nhaynes84/roam/roam-touch/cad/out/bracer_pack_shot_iso.png

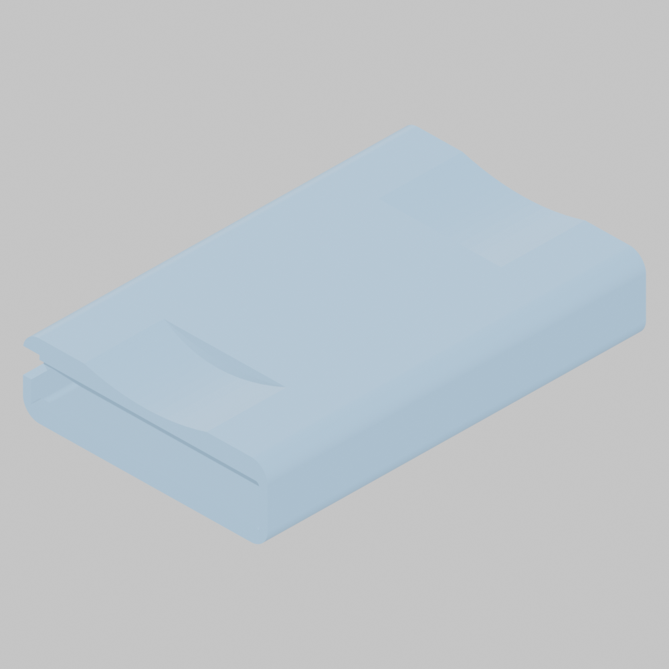
roam-touch/cad/out/bracer_pack_shot_iso.png
