nhaynes84/roam/roam-touch/cad/out/bracer_pack_shot_right.png

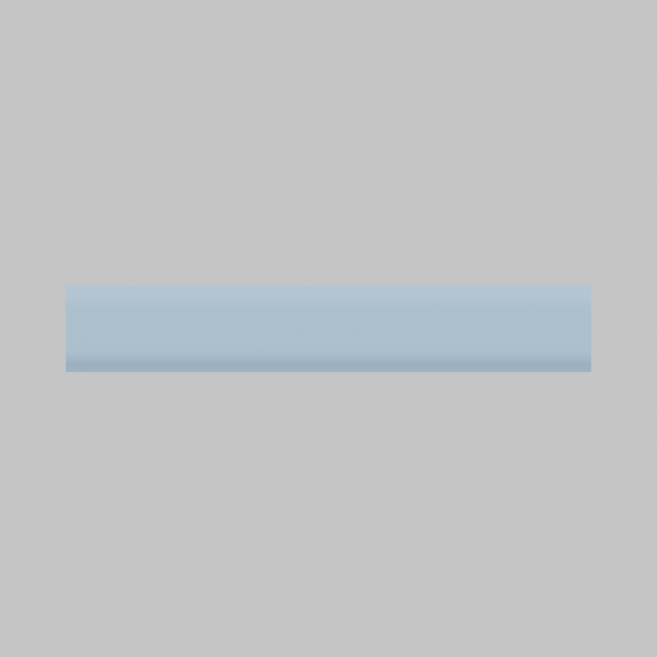
roam-touch/cad/out/bracer_pack_shot_right.png
