nhaynes84/roam/roam-touch/cad/out/bracer_pack_shot_top.png

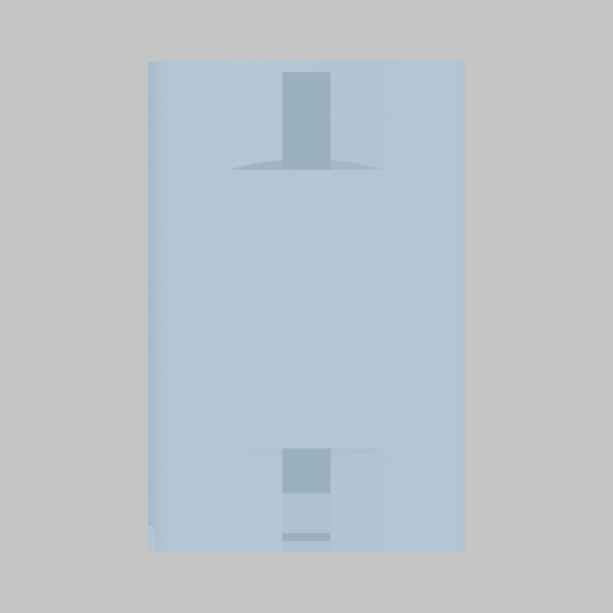
roam-touch/cad/out/bracer_pack_shot_top.png
