nhaynes84/roam/roam-touch/cad/out/landscape_shot_iso.png

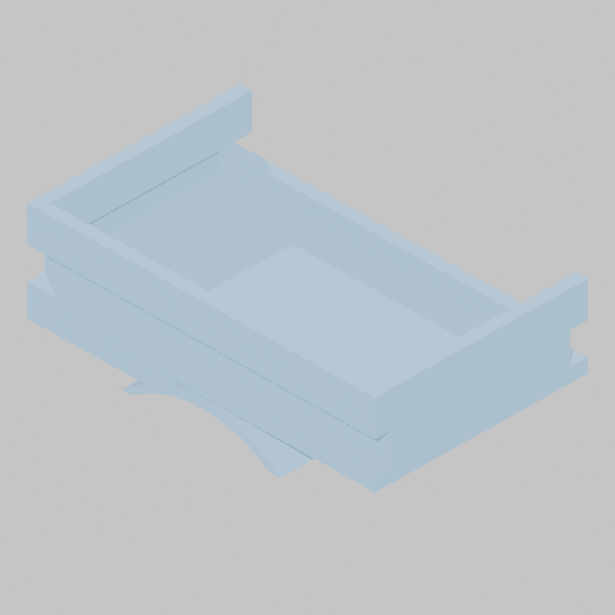
roam-touch/cad/out/landscape_shot_iso.png
