nhaynes84/roam/roam-touch/cad/out/landscape_shot_top.png

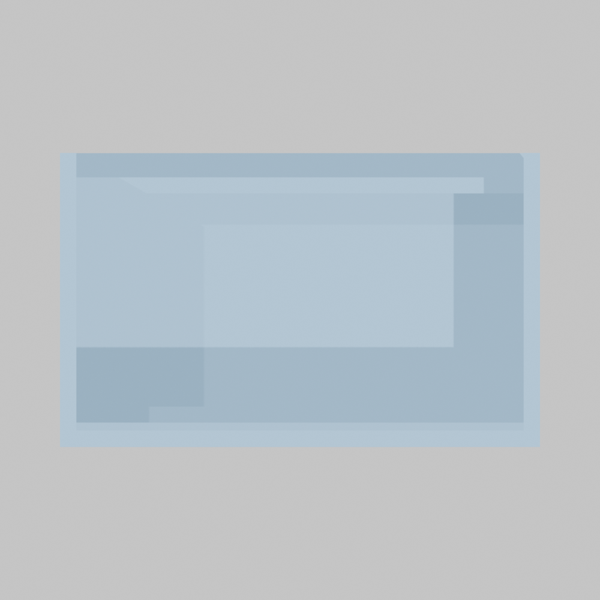
roam-touch/cad/out/landscape_shot_top.png
