nhaynes84/roam/roam-touch/cad/out/view_asm_bow.png

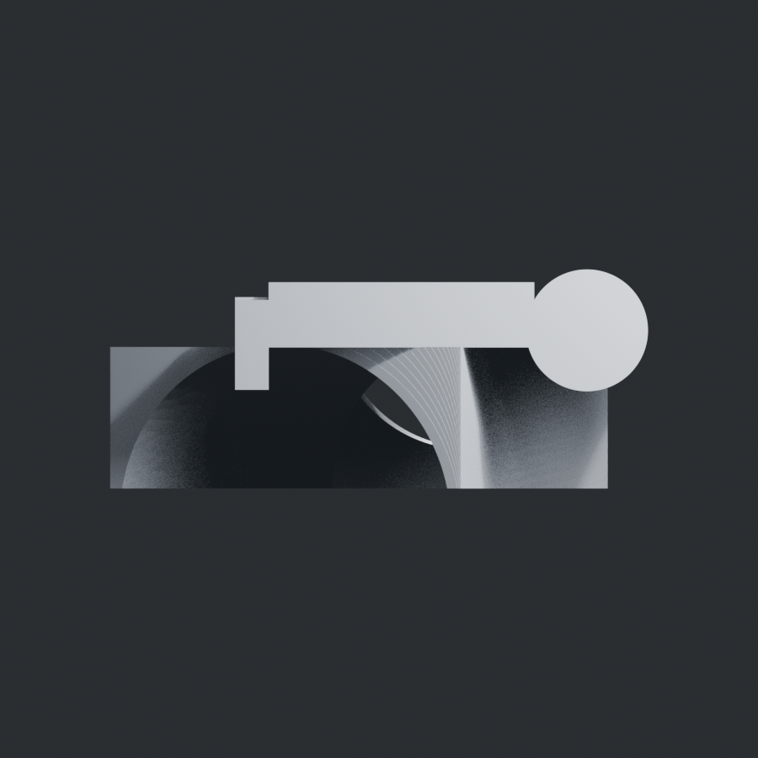
roam-touch/cad/out/view_asm_bow.png
