nhaynes84/roam/roam-touch/cad/out/view_asm_iso.png

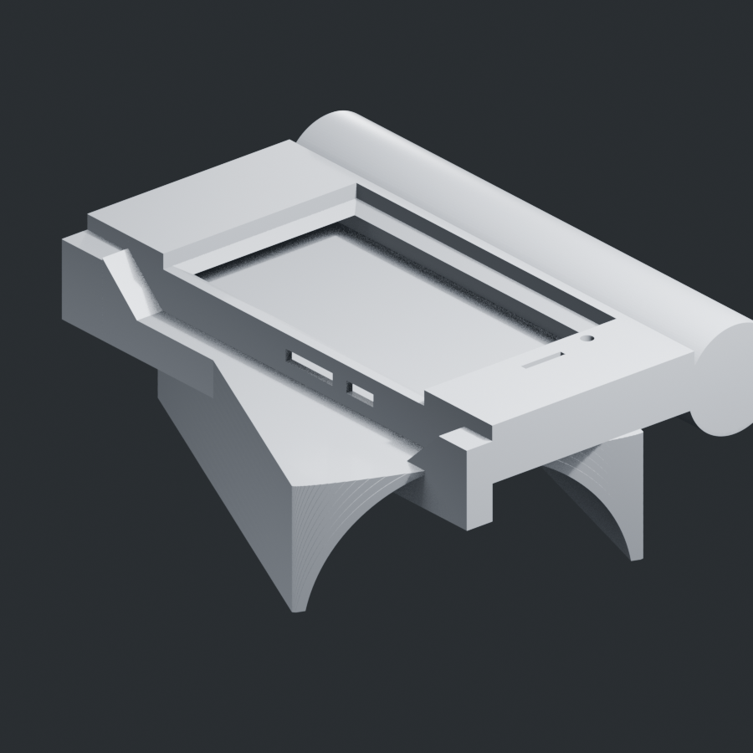
roam-touch/cad/out/view_asm_iso.png
