nhaynes84/roam/roam-touch/cad/out/view_asm_stbd.png

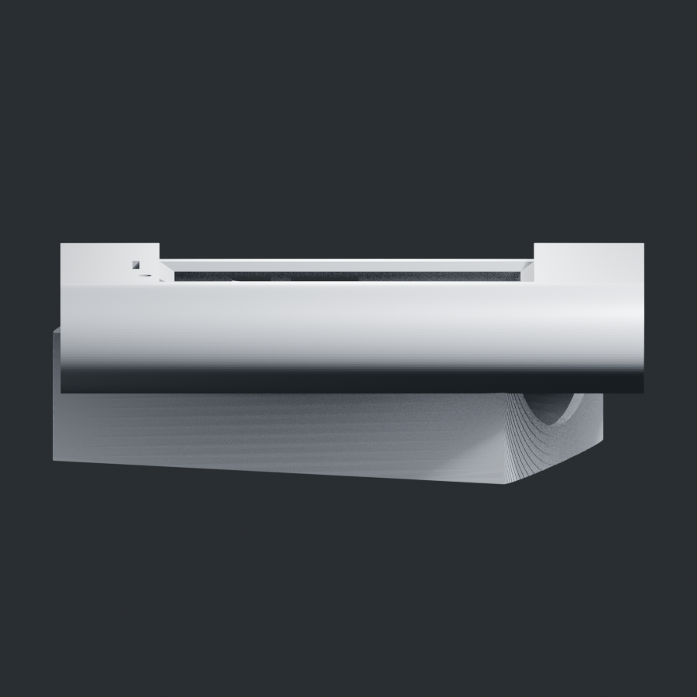
roam-touch/cad/out/view_asm_stbd.png
