nhaynes84/roam/roam-touch/cad/out/view_asm_stern.png

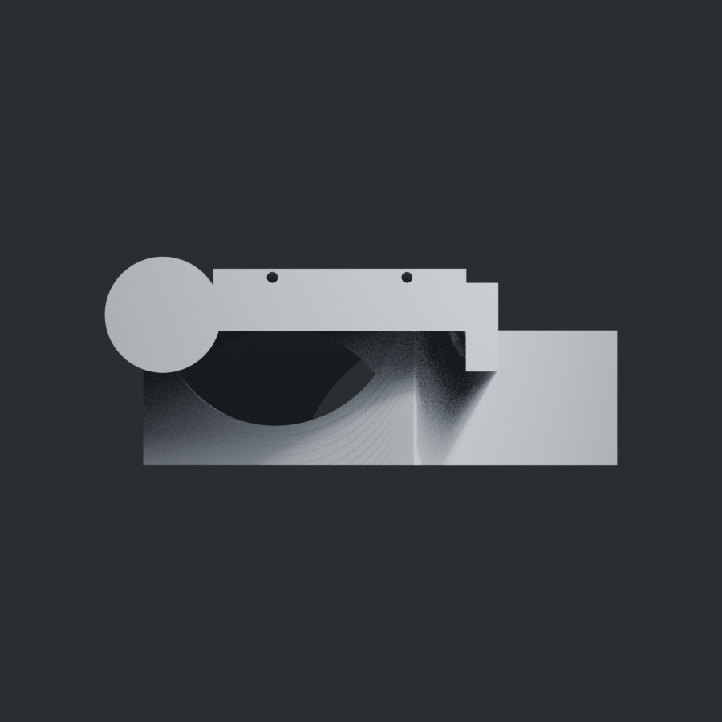
roam-touch/cad/out/view_asm_stern.png
