nhaynes84/roam/roam-touch/cad/out/view_asm_under.png

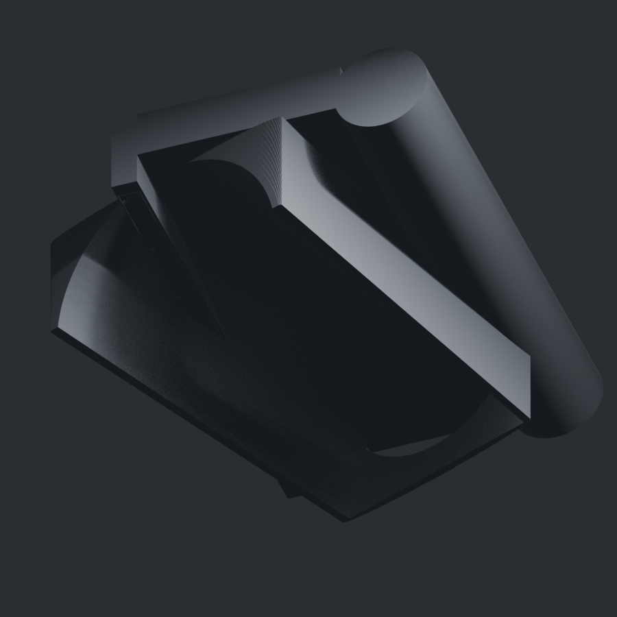
roam-touch/cad/out/view_asm_under.png
