nhaynes84/roam/roam-touch/cad/out/view_band_bow.png

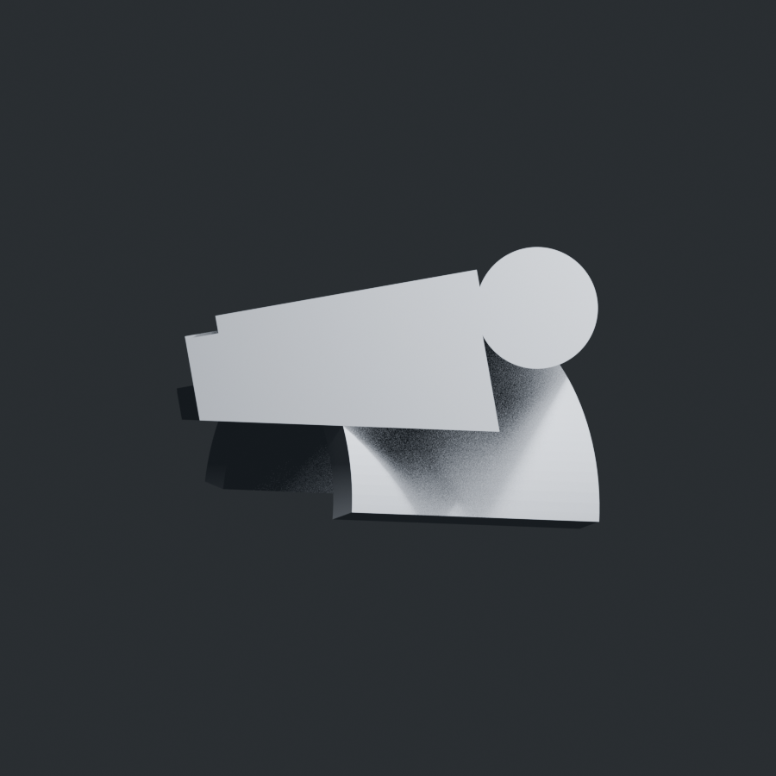
roam-touch/cad/out/view_band_bow.png
