nhaynes84/roam/roam-touch/cad/out/view_band_end.png

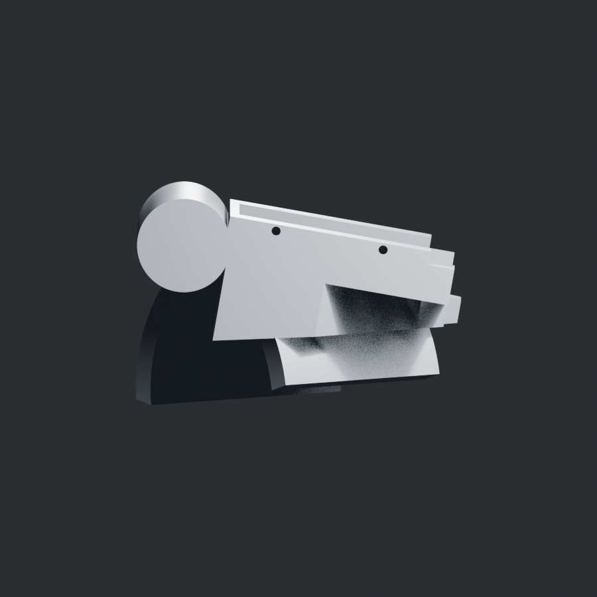
roam-touch/cad/out/view_band_end.png
