nhaynes84/roam/roam-touch/cad/out/view_band_iso.png

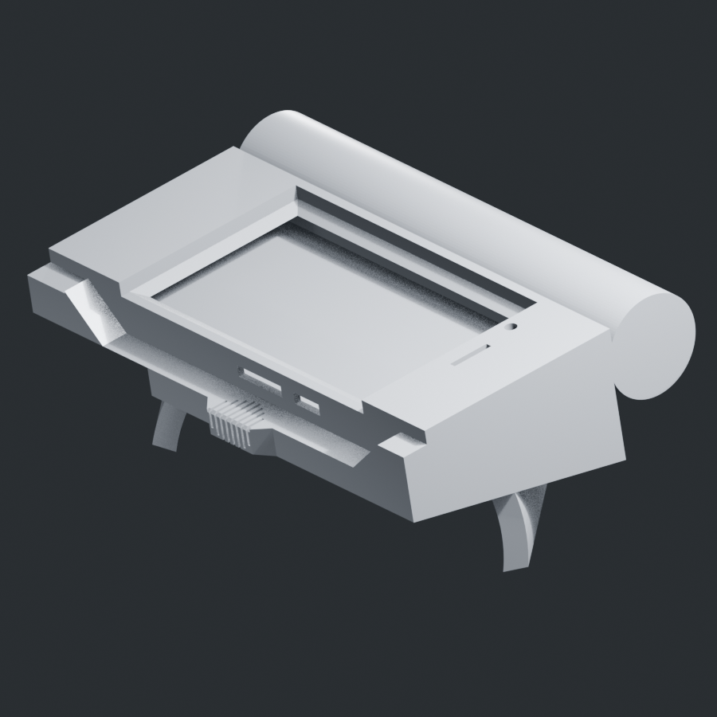
roam-touch/cad/out/view_band_iso.png
