nhaynes84/roam/roam-touch/cad/out/view_cap.png

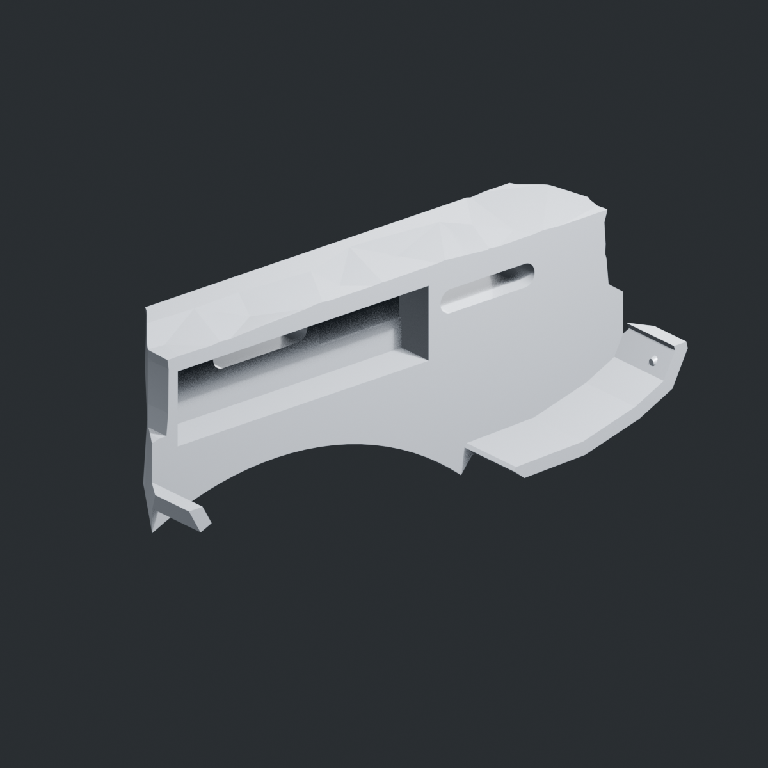
roam-touch/cad/out/view_cap.png
