nhaynes84/roam/roam-touch/cad/out/view_cc_end.png

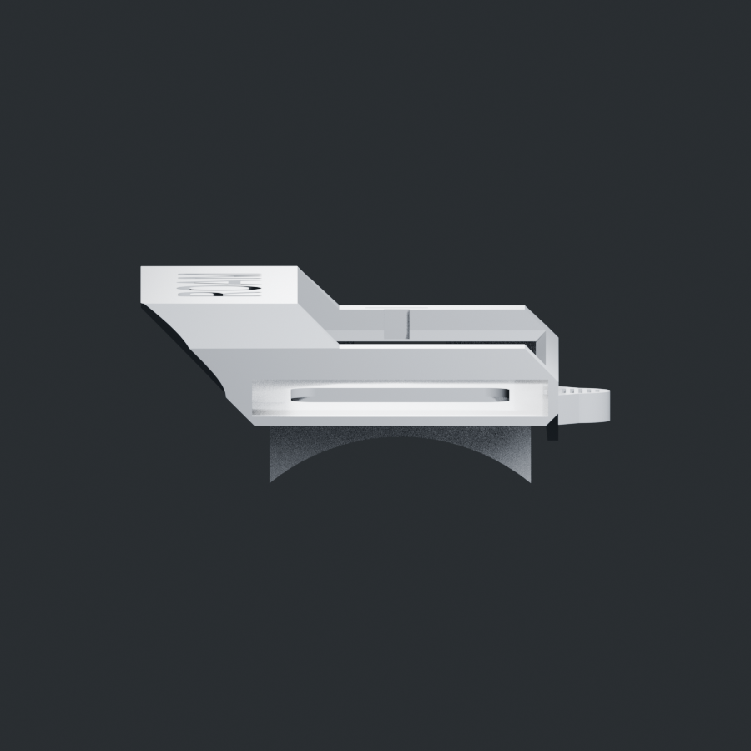
roam-touch/cad/out/view_cc_end.png
