nhaynes84/roam/roam-touch/cad/out/view_cc_iso.png

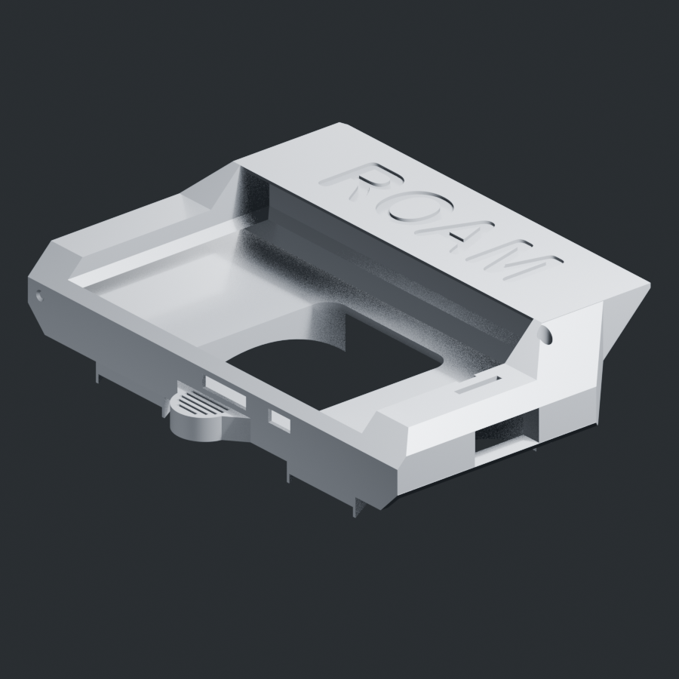
roam-touch/cad/out/view_cc_iso.png
