nhaynes84/roam/roam-touch/cad/out/view_cc_top.png

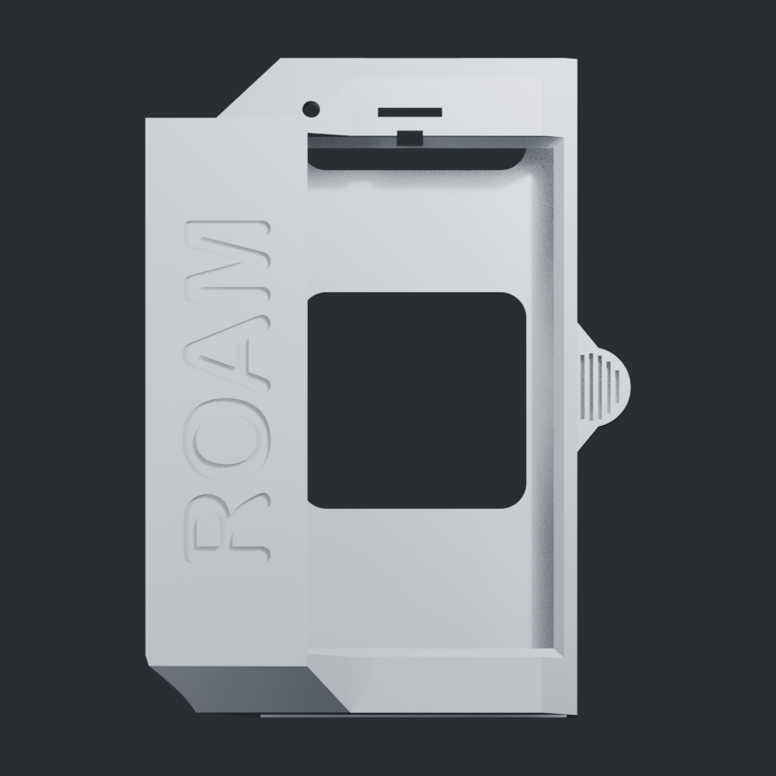
roam-touch/cad/out/view_cc_top.png
