nhaynes84/roam/roam-touch/cad/out/view_cov_open_e.png

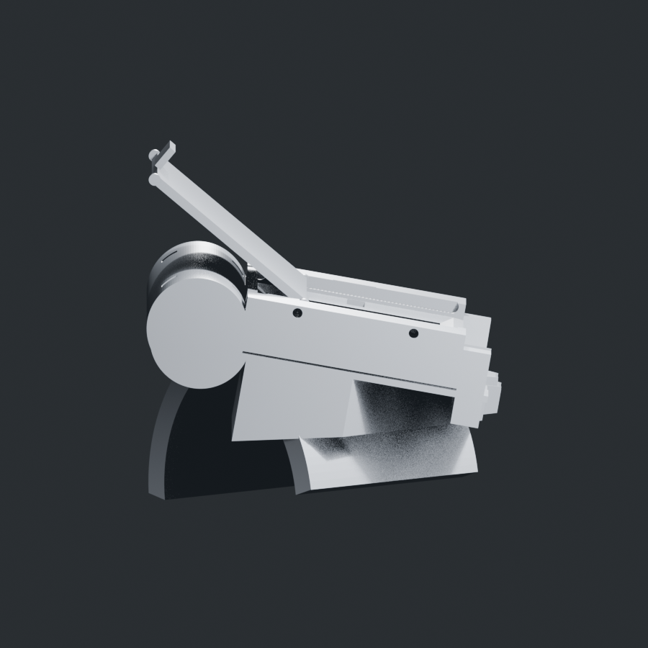
roam-touch/cad/out/view_cov_open_e.png
