nhaynes84/roam/roam-touch/cad/out/view_cov_open_i.png

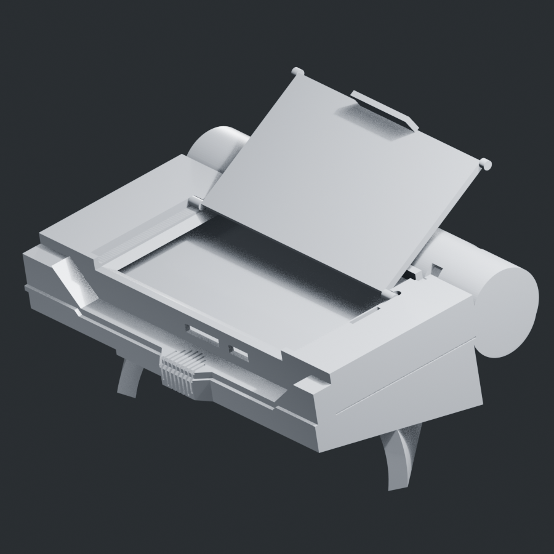
roam-touch/cad/out/view_cov_open_i.png
