nhaynes84/roam/roam-touch/cad/out/view_cuff_bow.png

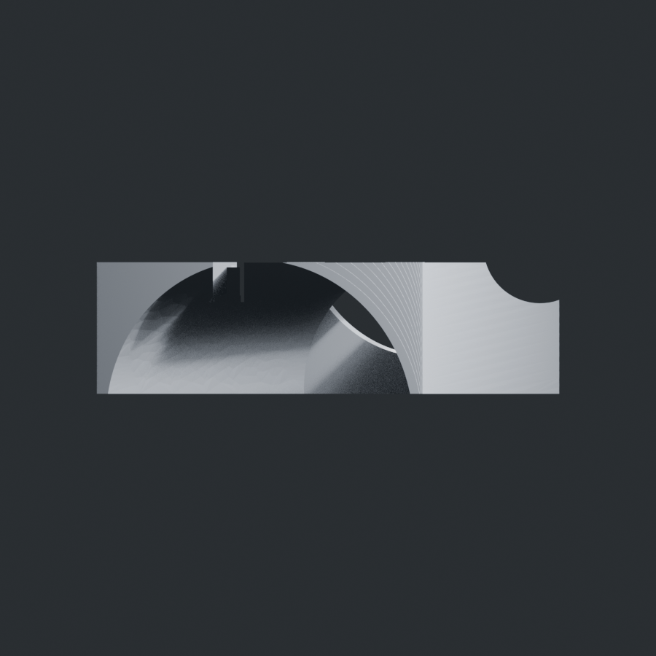
roam-touch/cad/out/view_cuff_bow.png
