nhaynes84/roam/roam-touch/cad/out/view_cuff_iso.png

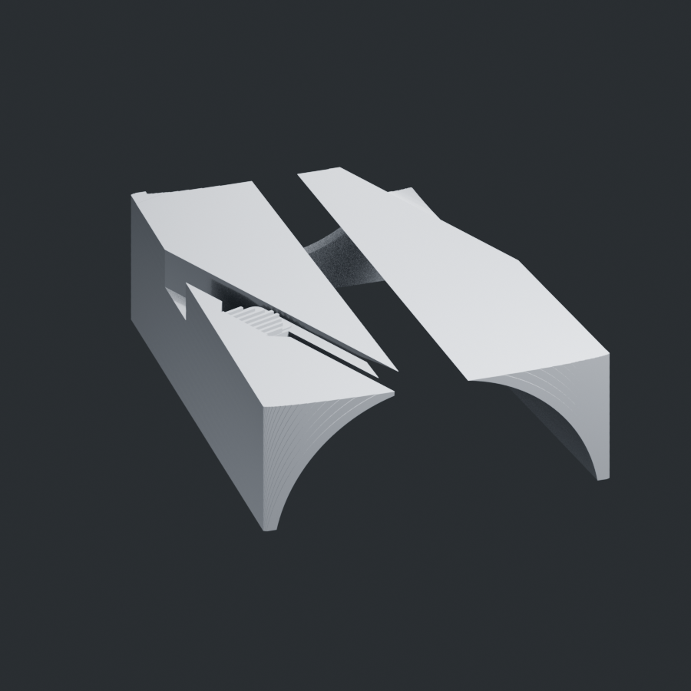
roam-touch/cad/out/view_cuff_iso.png
