nhaynes84/roam/roam-touch/cad/out/view_end_elbow.png

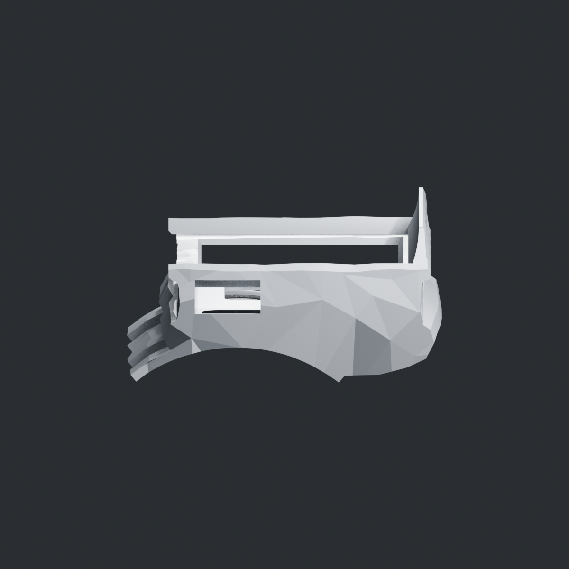
roam-touch/cad/out/view_end_elbow.png
