nhaynes84/roam/roam-touch/cad/out/view_end_elbow_q.png

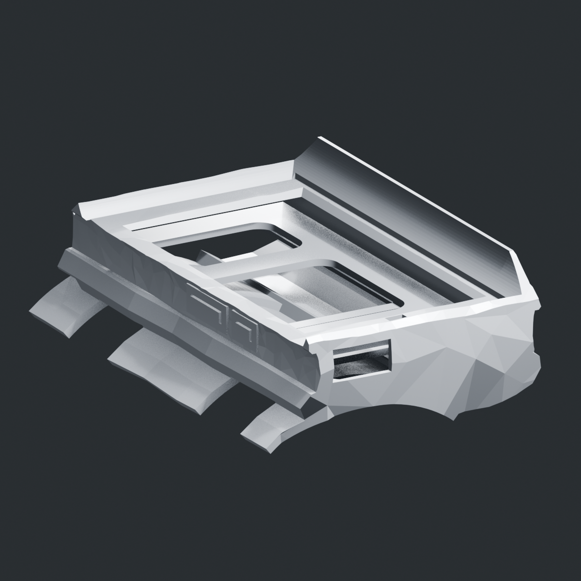
roam-touch/cad/out/view_end_elbow_q.png
