nhaynes84/roam/roam-touch/cad/out/view_end_wrist.png

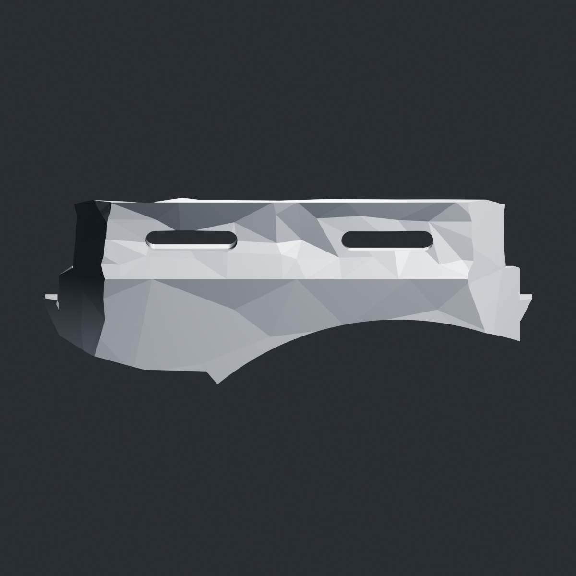
roam-touch/cad/out/view_end_wrist.png
