nhaynes84/roam/roam-touch/cad/out/view_guard_side.png

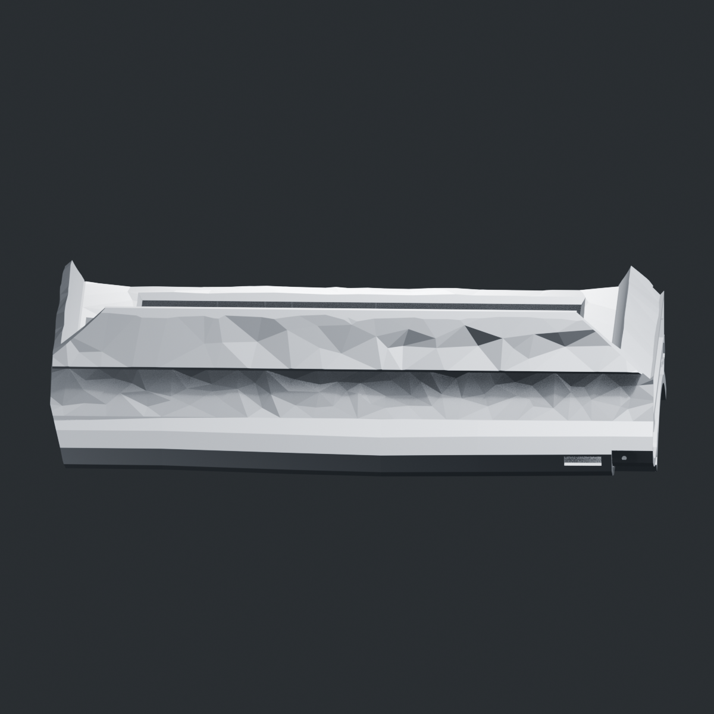
roam-touch/cad/out/view_guard_side.png
