nhaynes84/roam/roam-touch/cad/out/view_hg_iso.png

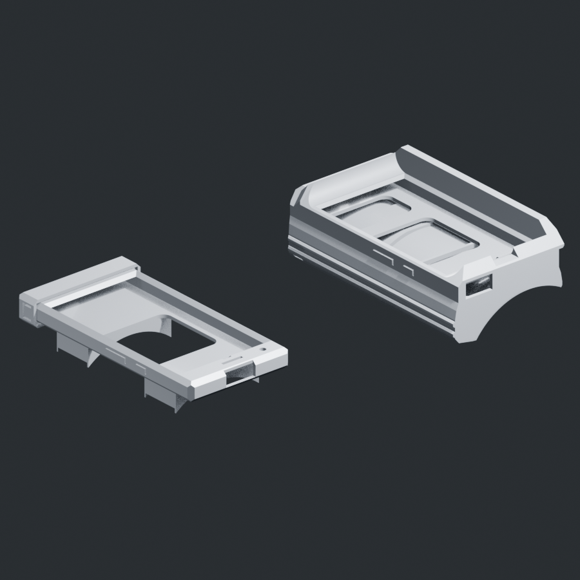
roam-touch/cad/out/view_hg_iso.png
