nhaynes84/roam/roam-touch/cad/out/view_hg_top.png

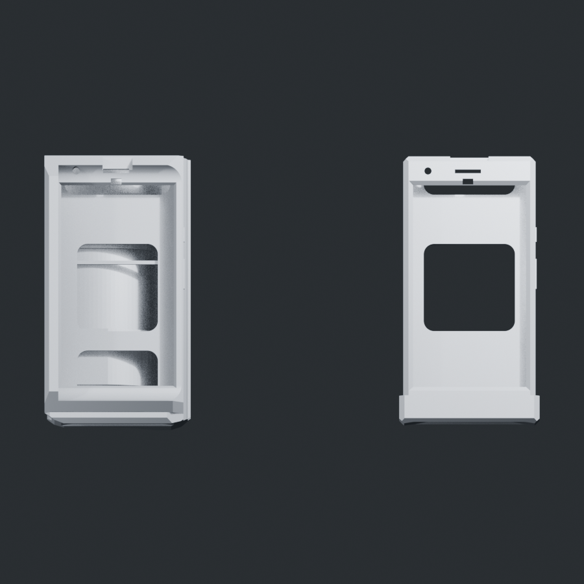
roam-touch/cad/out/view_hg_top.png
