nhaynes84/roam/roam-touch/cad/out/view_mic_q.png

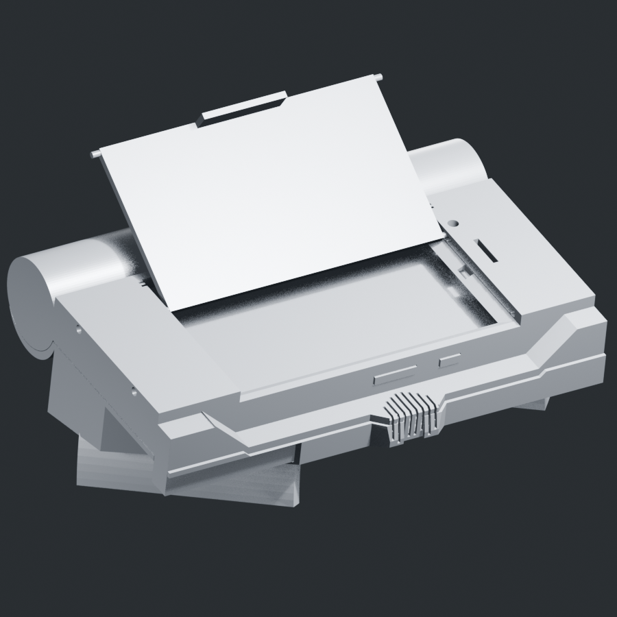
roam-touch/cad/out/view_mic_q.png
