nhaynes84/roam/roam-touch/cad/out/view_mic_sb.png

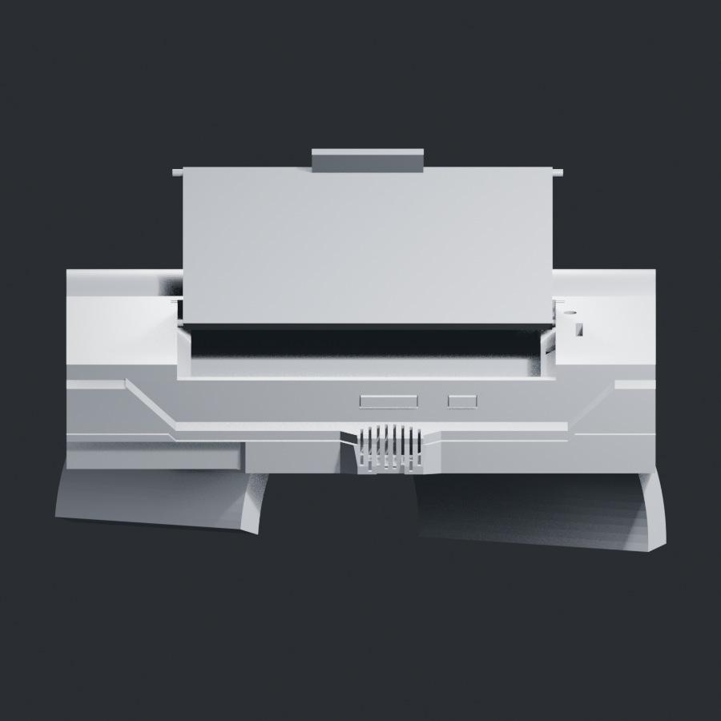
roam-touch/cad/out/view_mic_sb.png
