nhaynes84/roam/roam-touch/cad/out/view_pack_iso.png

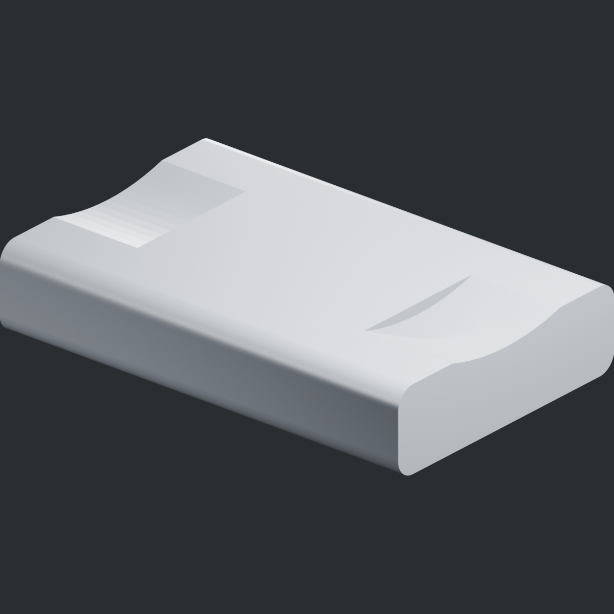
roam-touch/cad/out/view_pack_iso.png
