nhaynes84/roam/roam-touch/cad/out/view_roam1_btn.png

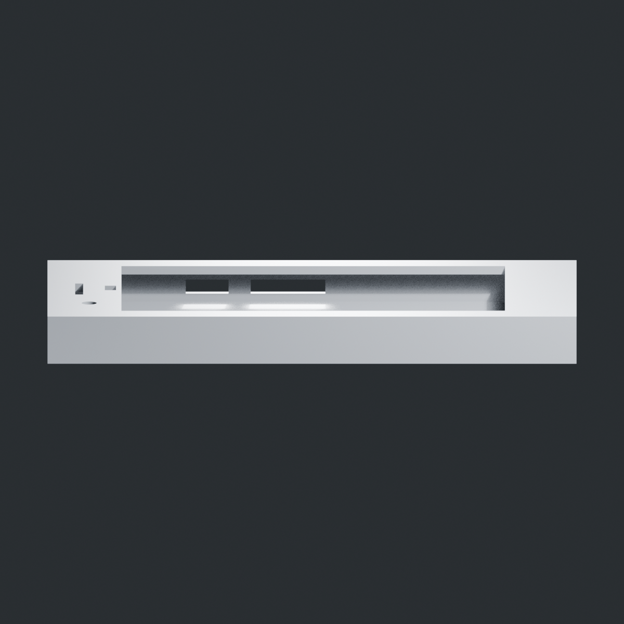
roam-touch/cad/out/view_roam1_btn.png
