nhaynes84/roam/roam-touch/cad/out/view_roam1_iso.png

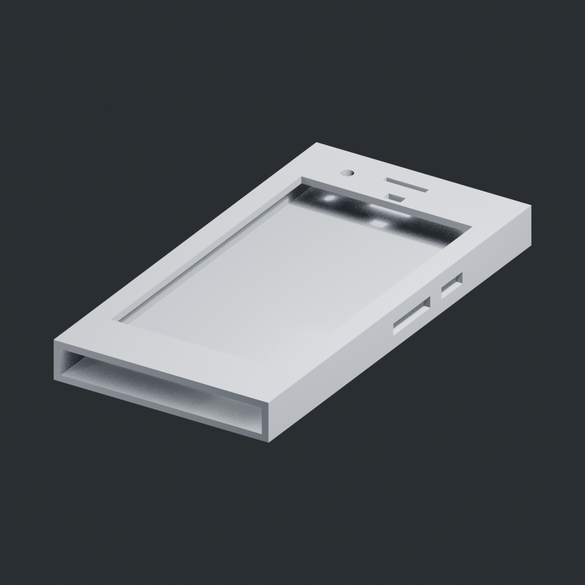
roam-touch/cad/out/view_roam1_iso.png
