nhaynes84/roam/roam-touch/cad/out/view_roam1_jack.png

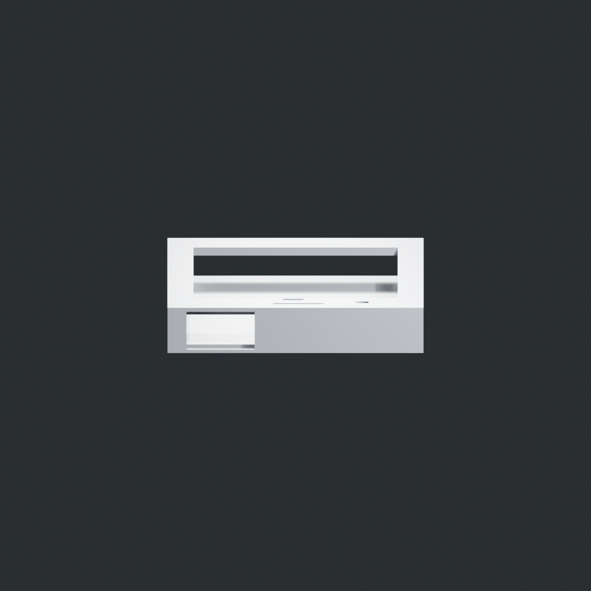
roam-touch/cad/out/view_roam1_jack.png
