nhaynes84/roam/roam-touch/cad/out/view_roam1_top.png

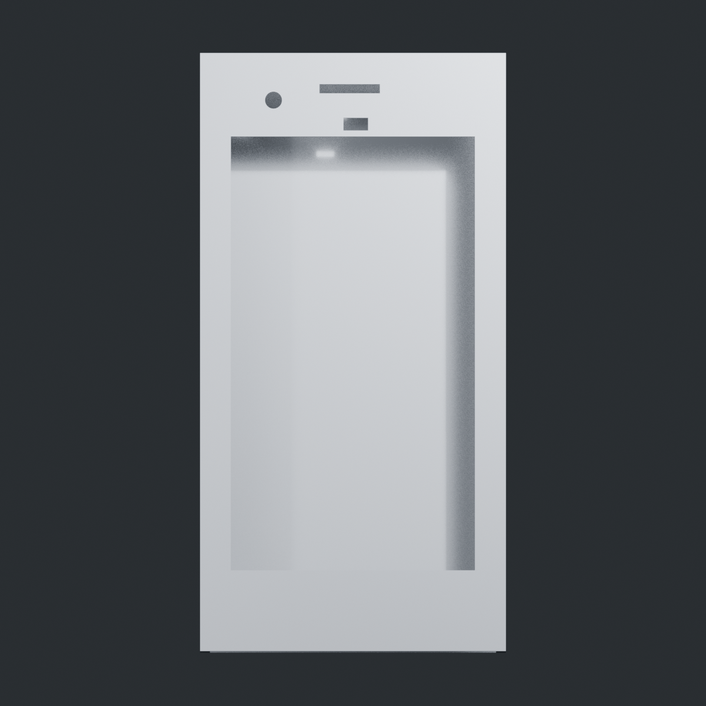
roam-touch/cad/out/view_roam1_top.png
