nhaynes84/roam/roam-touch/cad/out/view_roam1_usb.png

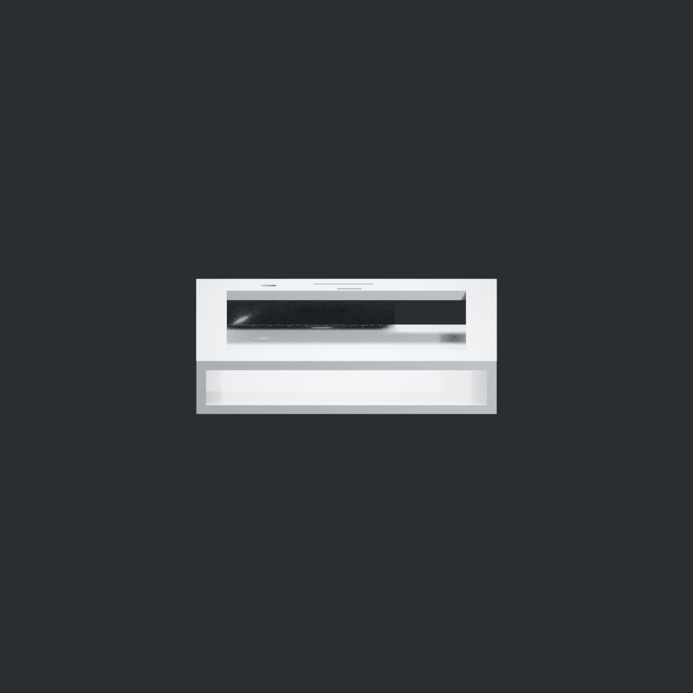
roam-touch/cad/out/view_roam1_usb.png
