nhaynes84/roam/roam-touch/cad/out/view_roam2_end.png

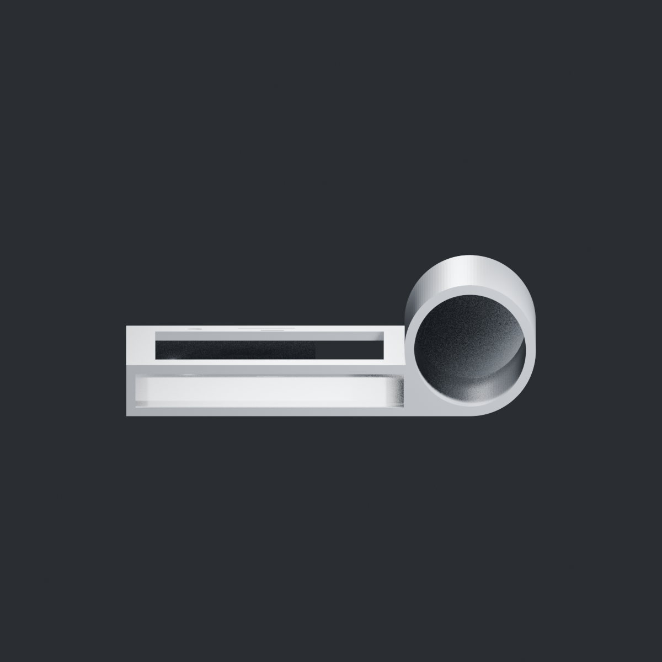
roam-touch/cad/out/view_roam2_end.png
