nhaynes84/roam/roam-touch/cad/out/view_roam2_iso.png

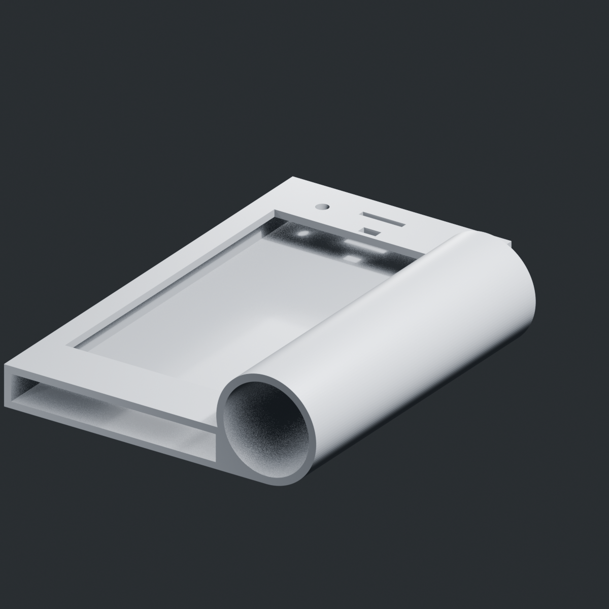
roam-touch/cad/out/view_roam2_iso.png
