nhaynes84/roam/roam-touch/cad/out/view_roam2_top.png

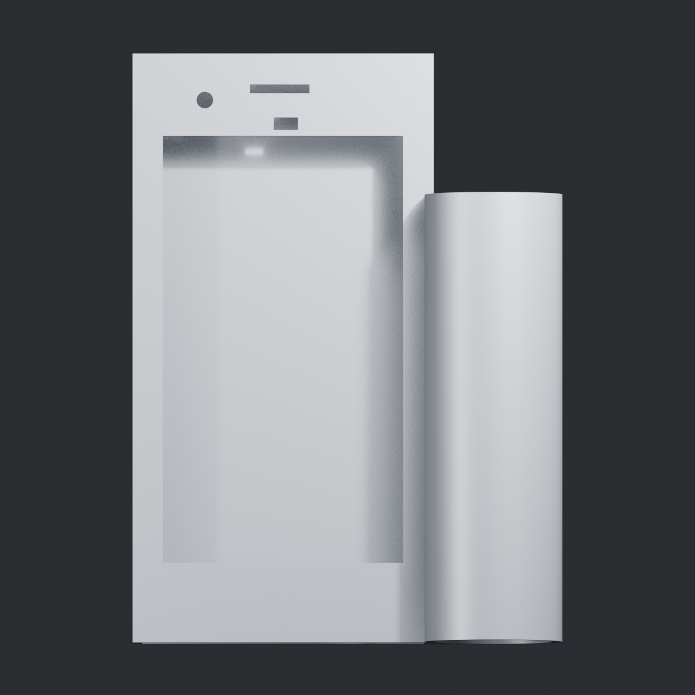
roam-touch/cad/out/view_roam2_top.png
