nhaynes84/roam/roam-touch/cad/out/view_roam2_worn.png

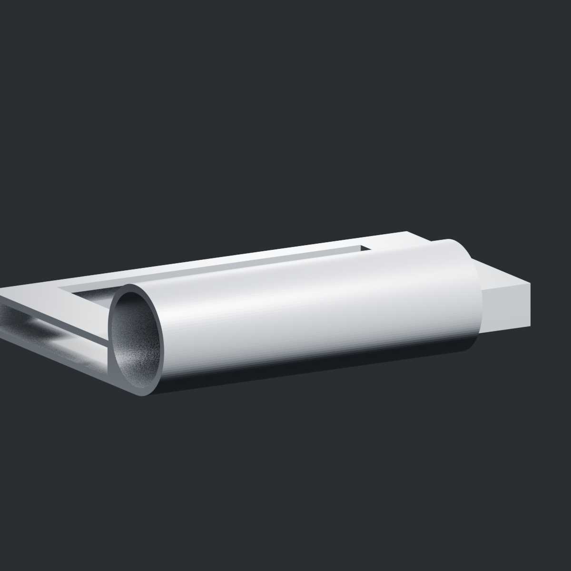
roam-touch/cad/out/view_roam2_worn.png
