nhaynes84/roam/roam-touch/cad/out/view_roam3_end.png

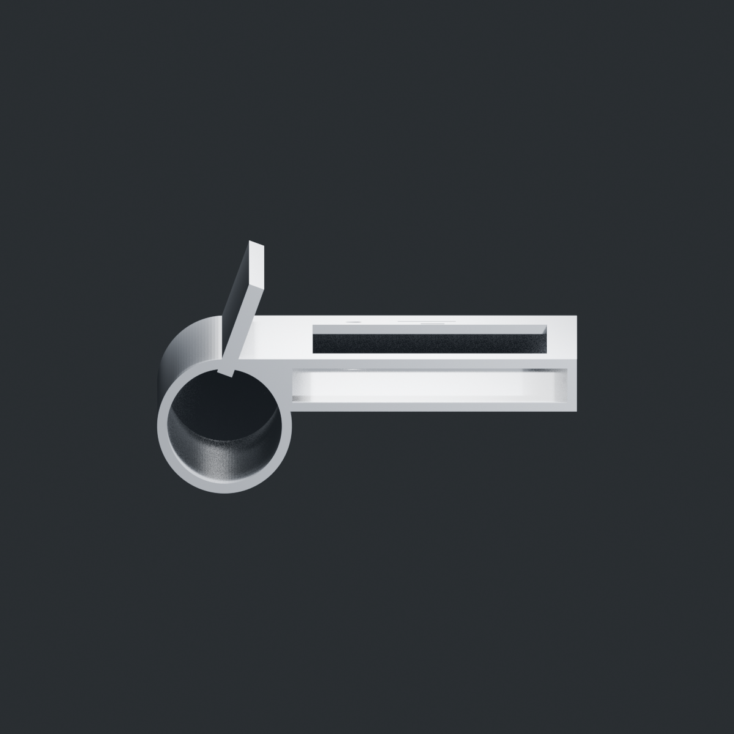
roam-touch/cad/out/view_roam3_end.png
