nhaynes84/roam/roam-touch/cad/out/view_roam3_iso.png

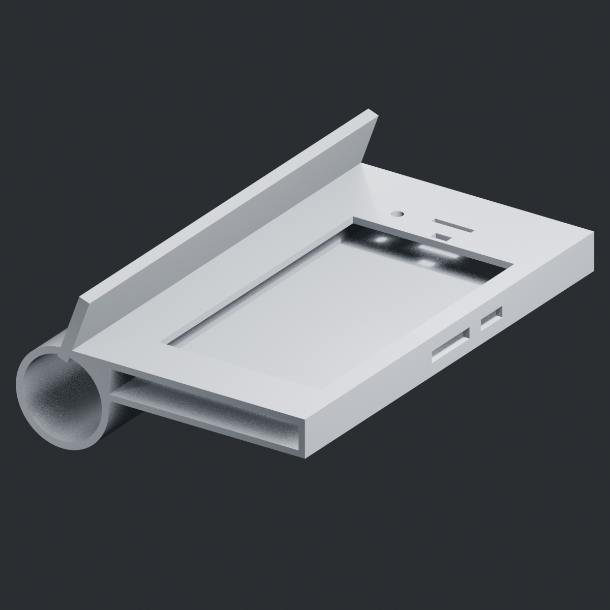
roam-touch/cad/out/view_roam3_iso.png
