nhaynes84/roam/roam-touch/cad/out/view_roam3_worn.png

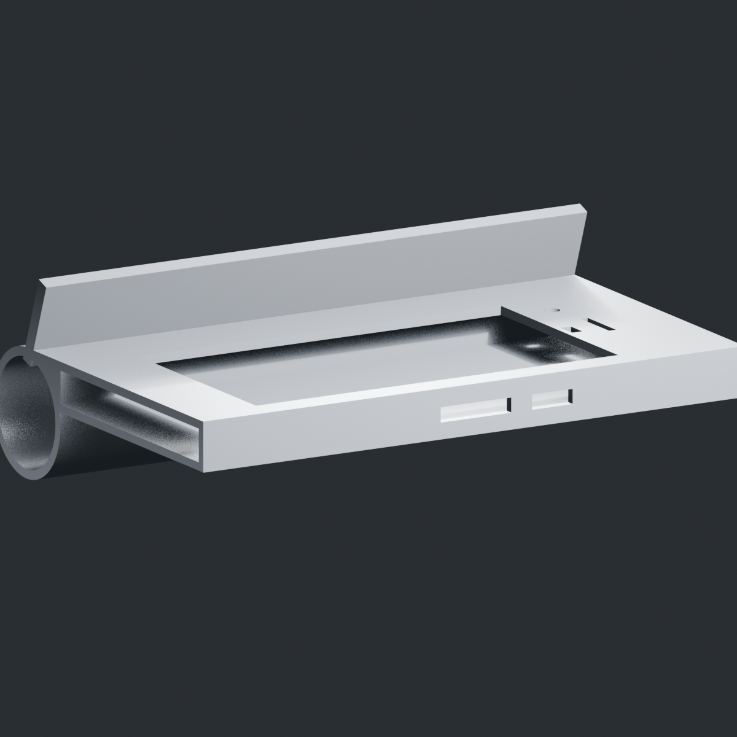
roam-touch/cad/out/view_roam3_worn.png
