nhaynes84/roam/roam-touch/cad/out/view_slots_i.png

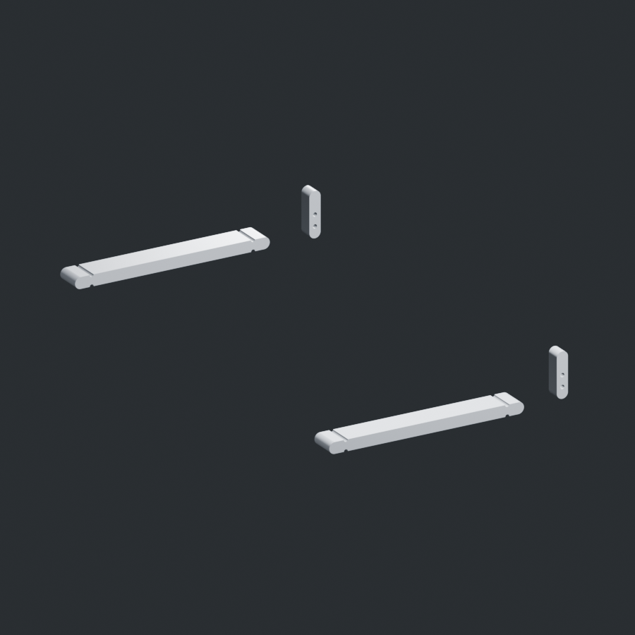
roam-touch/cad/out/view_slots_i.png
