nhaynes84/roam/roam-touch/cad/out/view_top.png

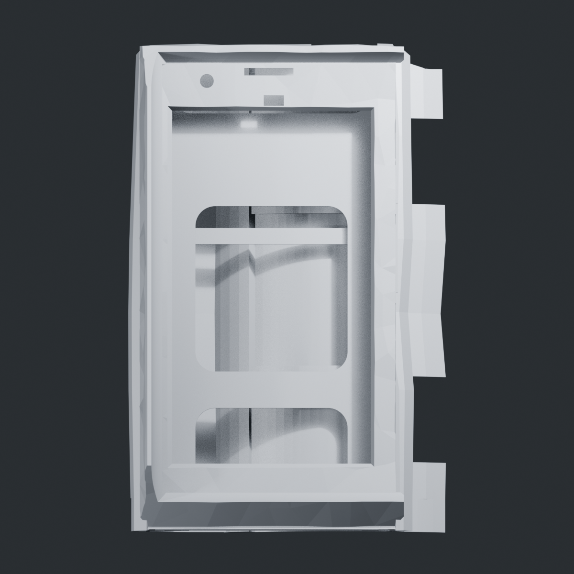
roam-touch/cad/out/view_top.png
