nhaynes84/roam/roam-touch/cad/out/view_wall_e.png

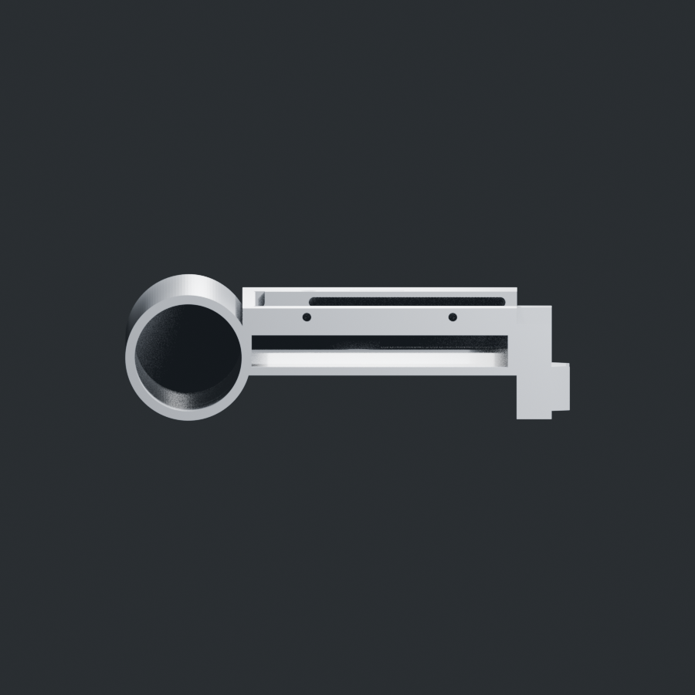
roam-touch/cad/out/view_wall_e.png
