nhaynes84/roam/roam-touch/cad/out/view_wall_q.png

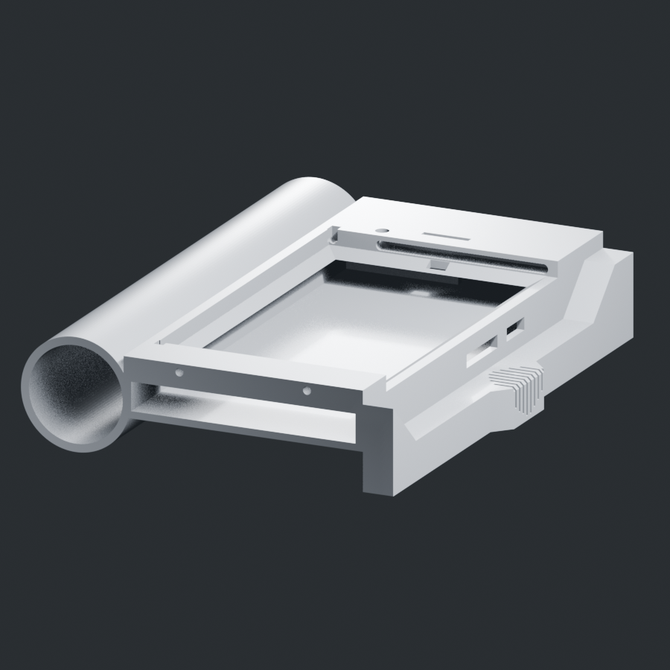
roam-touch/cad/out/view_wall_q.png
