nhaynes84/roam/roam-touch/cad/out/view_worn_bow.png

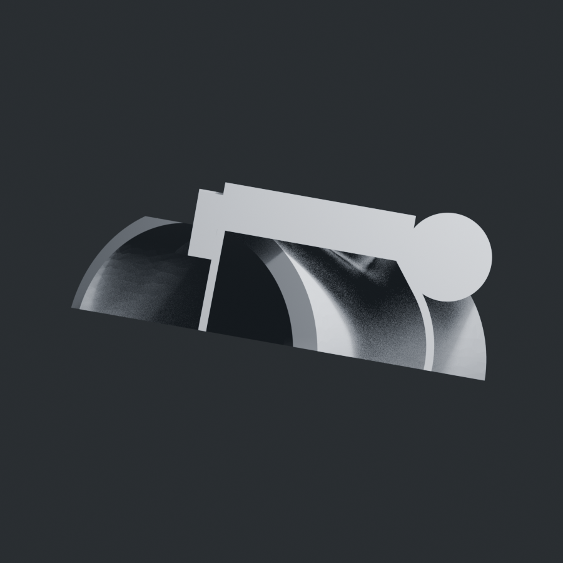
roam-touch/cad/out/view_worn_bow.png
