nhaynes84/roam/roam-touch/cad/out/view_worn_iso2.png

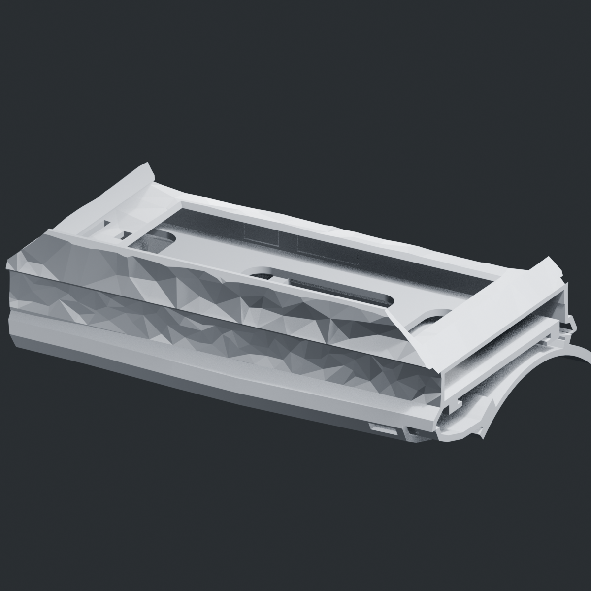
roam-touch/cad/out/view_worn_iso2.png
