nhaynes84/roam/roam-touch/cad/out/view_worn_under.png

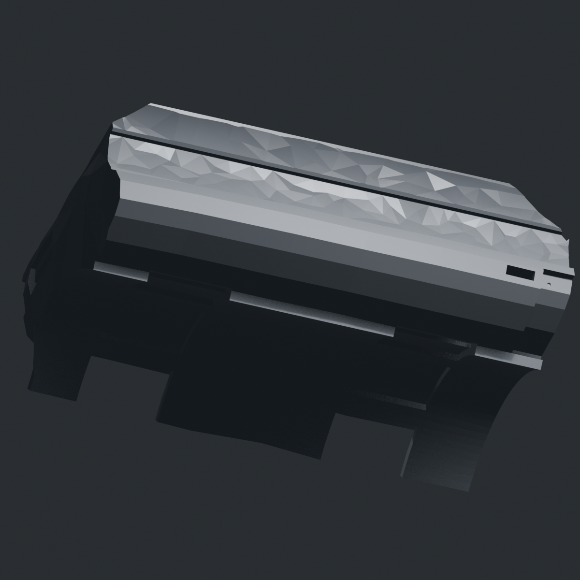
roam-touch/cad/out/view_worn_under.png
