nhaynes84/roam/roam-touch/cad/ref/lowpoly-2-owls.png

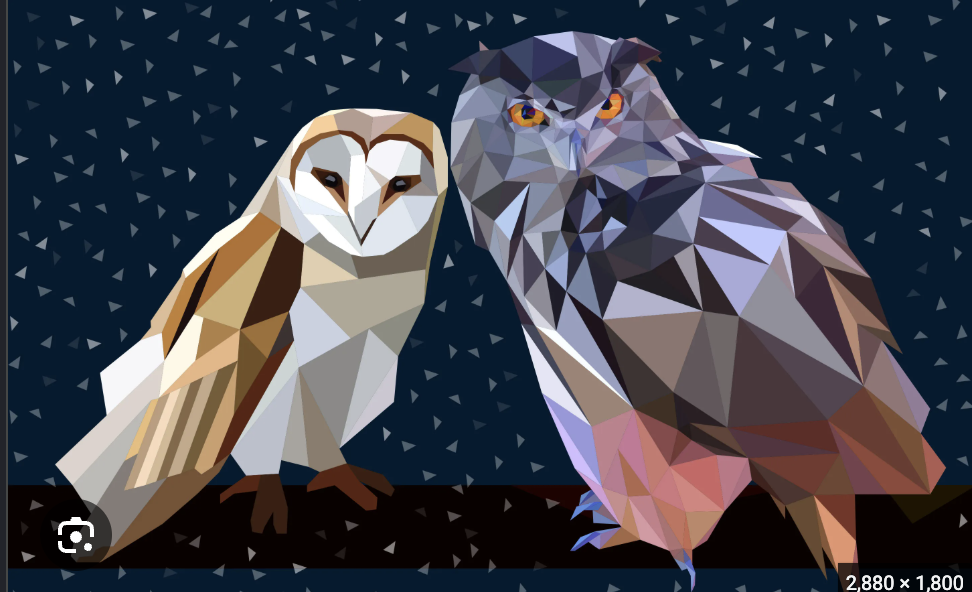
roam-touch/cad/ref/lowpoly-2-owls.png
