nhaynes84/roam/roam-touch/cad/ref/pipboy-visor-reference.png

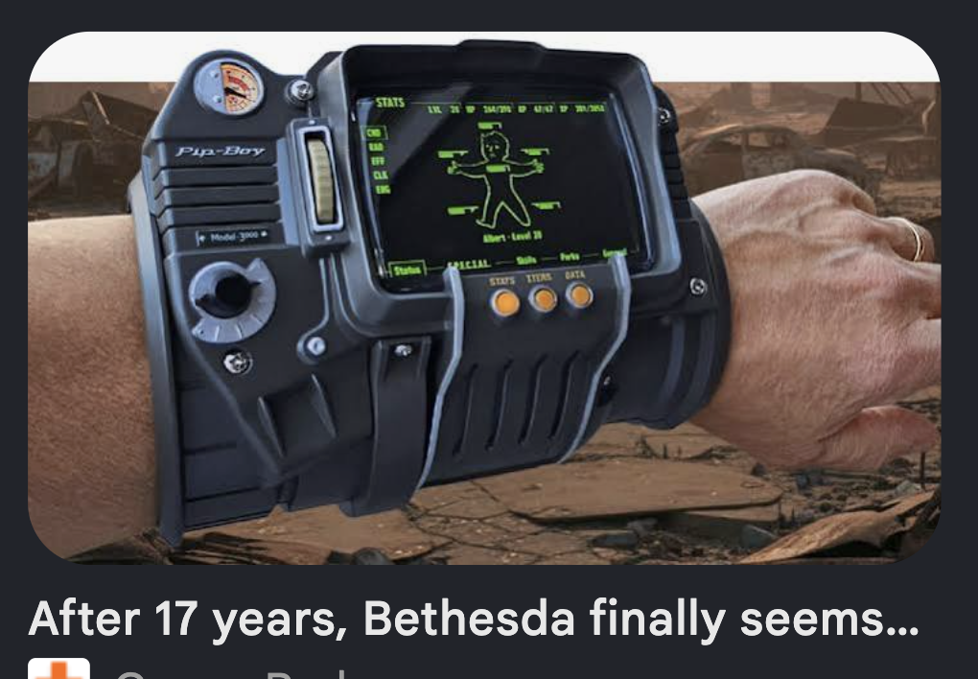
roam-touch/cad/ref/pipboy-visor-reference.png
