nhaynes84/roam/roam-touch/cad/out/roam_cover_shut.stl

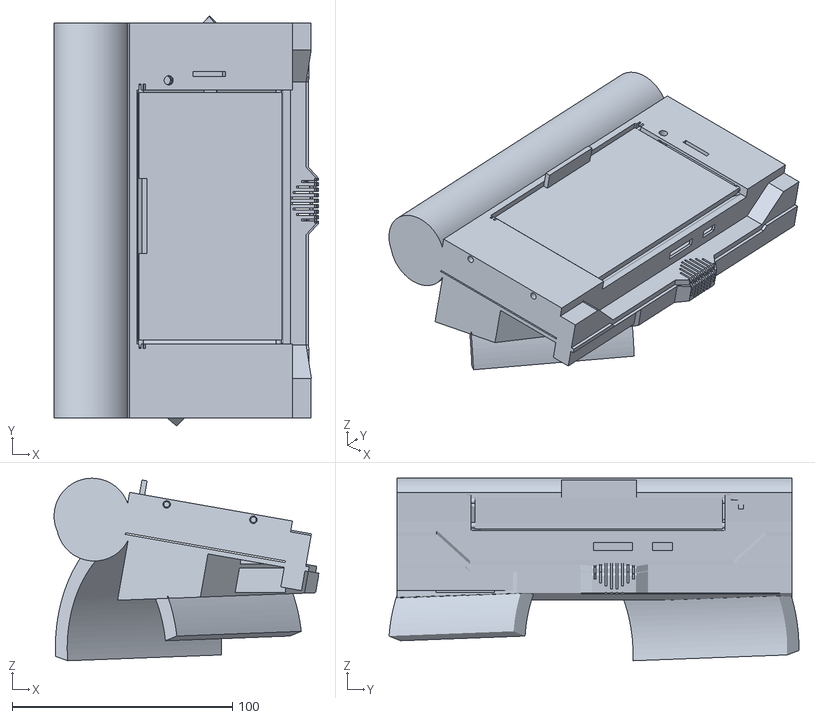
[picture p73: CAD file, 2026-08-20]
roam-touch/cad/out/roam_cover_shut.stl
120.2 x 186.2 x 82.9
