nhaynes84/roam/roam-touch/cad/out/roam_step3.step

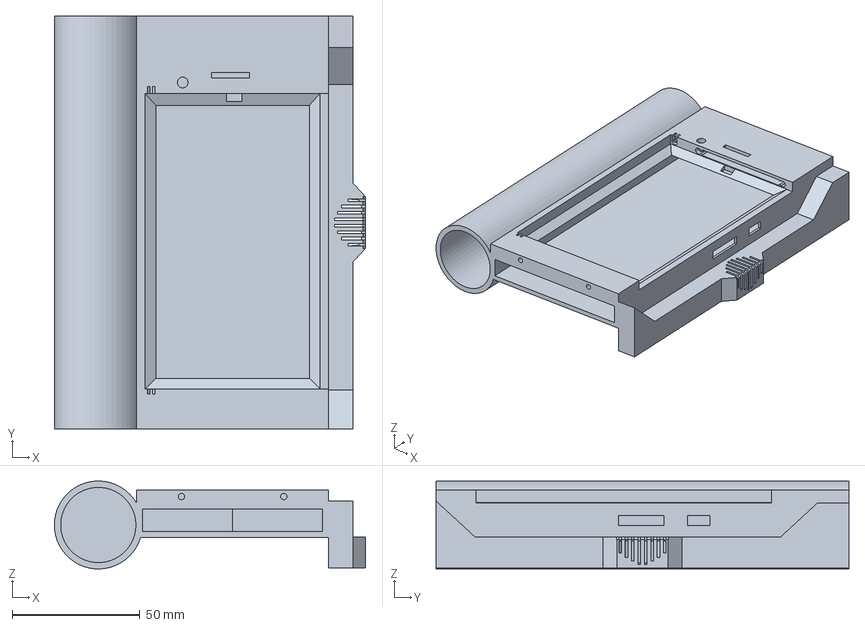
[picture p74: CAD file, 2026-08-20]
roam-touch/cad/out/roam_step3.step
121.7 x 161.4 x 34.4 mm
