nhaynes84/roam/roam-touch/cad/out/sample_band.stl

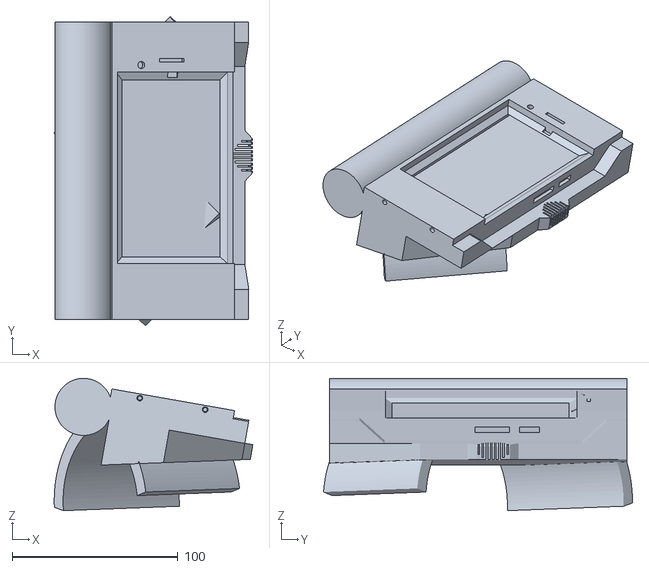
[picture p75: CAD file, 2026-08-20]
roam-touch/cad/out/sample_band.stl
119.7 x 186.2 x 79.7
