nhaynes84/roam/roam-touch/cad/out/roam_sleeve.step

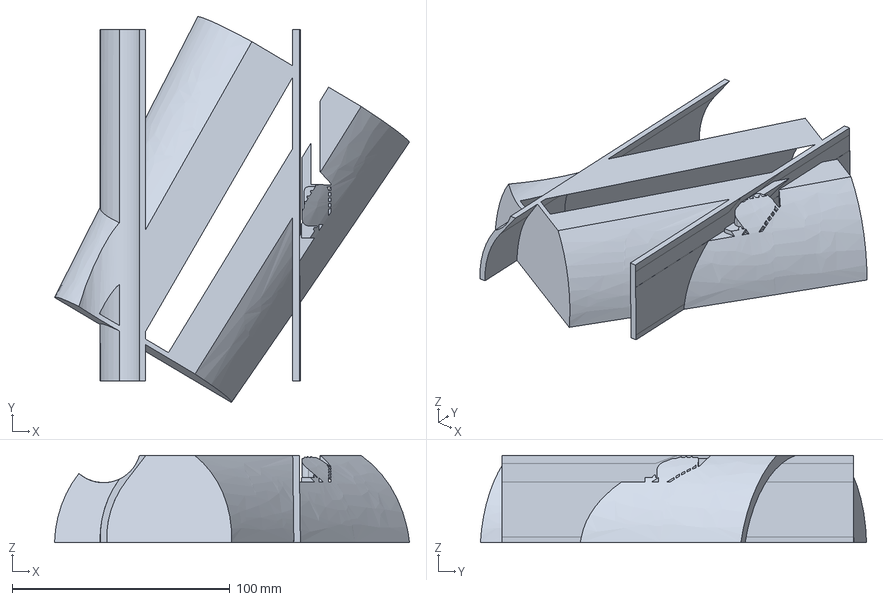
[picture p76: CAD file, 2026-08-20]
roam-touch/cad/out/roam_sleeve.step
163.1 x 177.4 x 40.0 mm
