nhaynes84/roam/roam-touch/cad/out/slots_only.stl

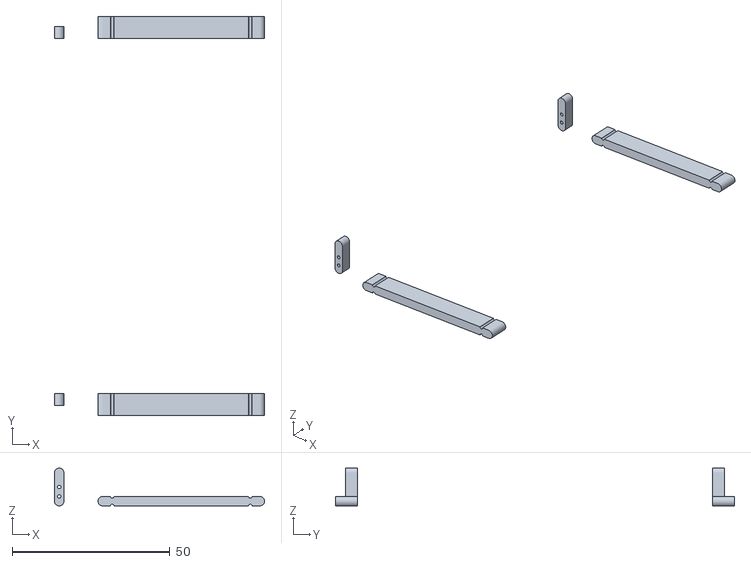
[picture p77: CAD file, 2026-08-20]
roam-touch/cad/out/slots_only.stl
66.6 x 126.5 x 12.0
