nhaynes84/roam/roam-touch/cad/out/roam_cover_open.stl

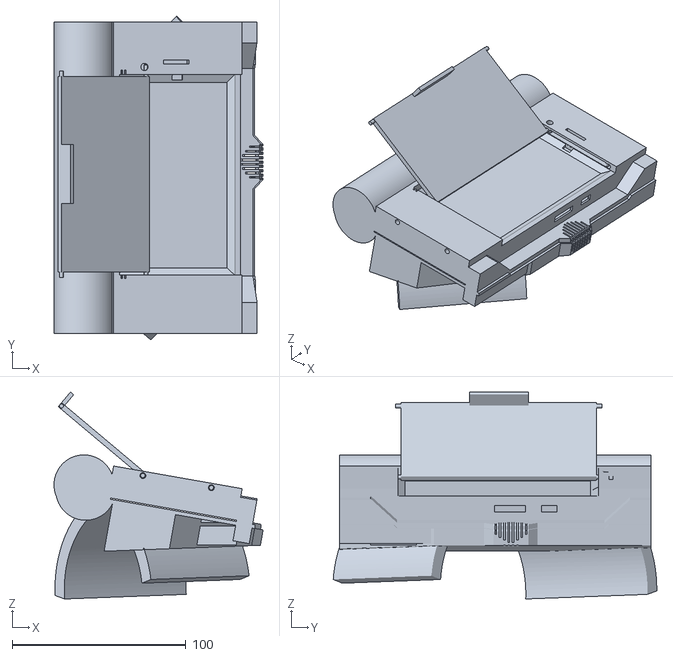
[picture p78: CAD file, 2026-08-20]
roam-touch/cad/out/roam_cover_open.stl
120.2 x 186.2 x 119.1
