nhaynes84/roam/roam-touch/cad/out/roam_step2.step

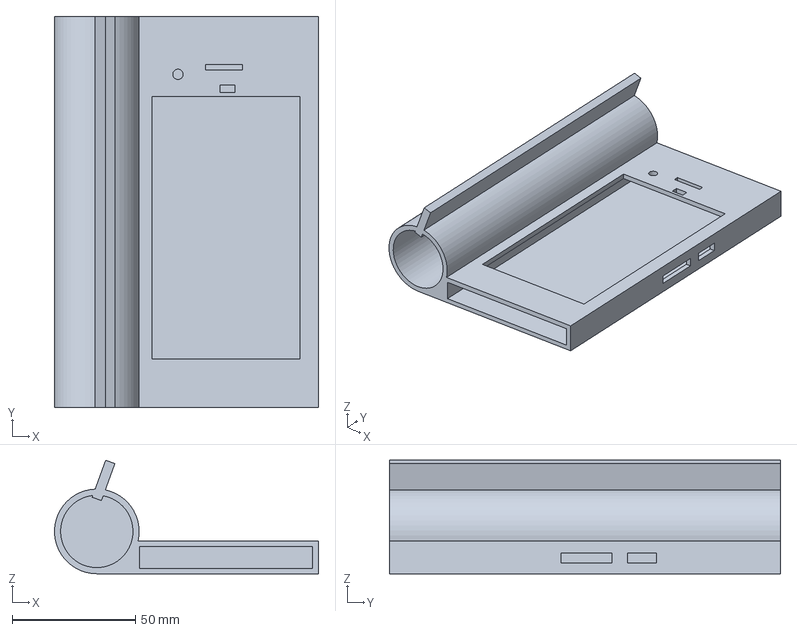
[picture p79: CAD file, 2026-08-14]
roam-touch/cad/out/roam_step2.step
107.2 x 159.0 x 46.1 mm
