nhaynes84/roam/roam-touch/cad/out/roam_step1.step

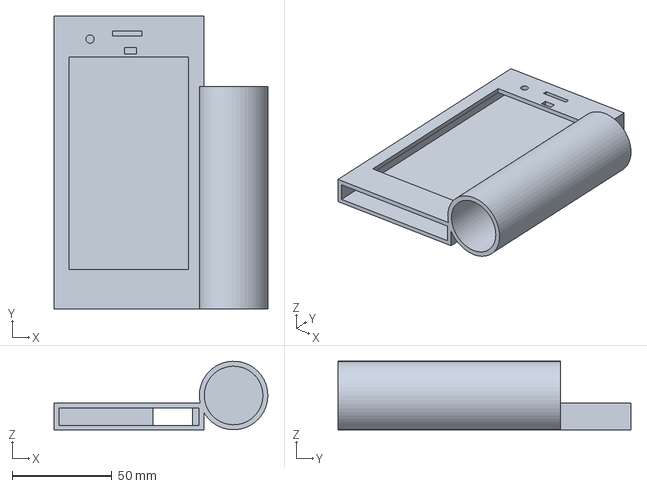
[picture p80: CAD file, 2026-08-13]
roam-touch/cad/out/roam_step1.step
107.2 x 147.0 x 34.4 mm
