nhaynes84/roam/roam-touch/cad/out/bracer_endcap.step

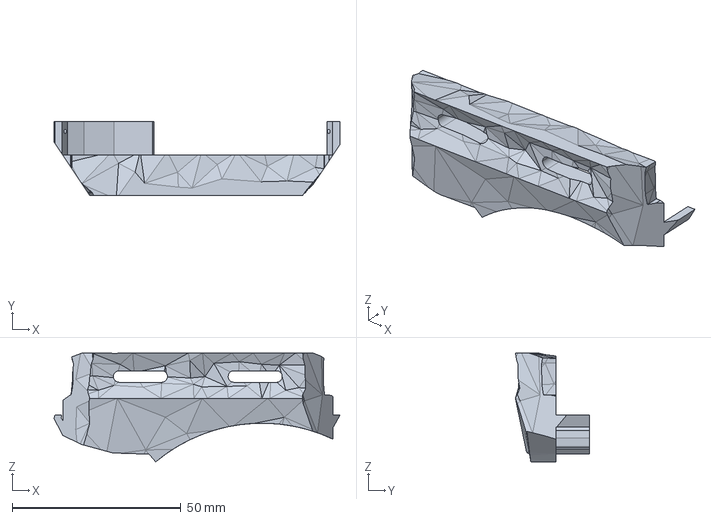
[picture p81: CAD file, 2026-08-13]
roam-touch/cad/out/bracer_endcap.step
84.7 x 22.0 x 32.2 mm
