nhaynes84/roam/roam-touch/cad/out/bracer_print.stl

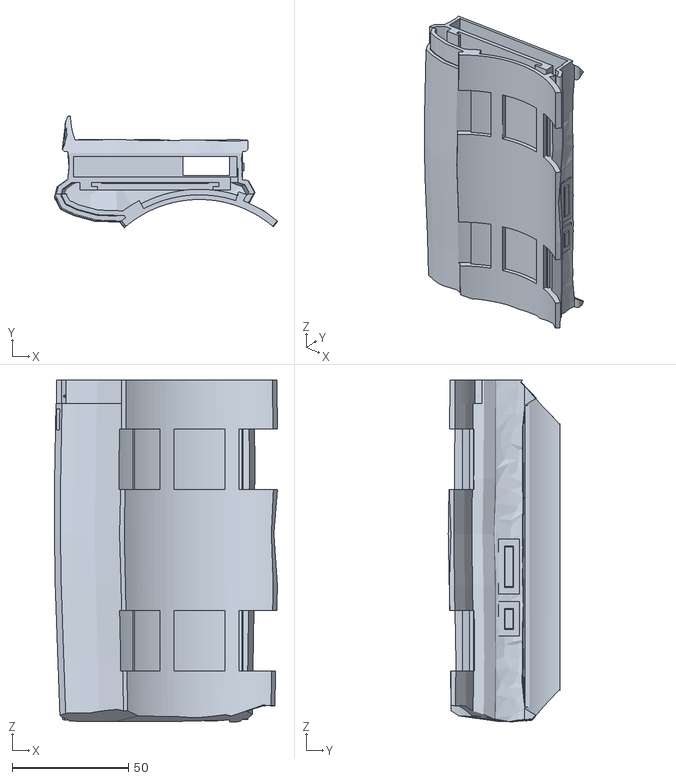
[picture p82: CAD file, 2026-08-13]
roam-touch/cad/out/bracer_print.stl
95.9 x 47.9 x 146.9
