nhaynes84/roam/roam-touch/cad/out/bracer_pack.step

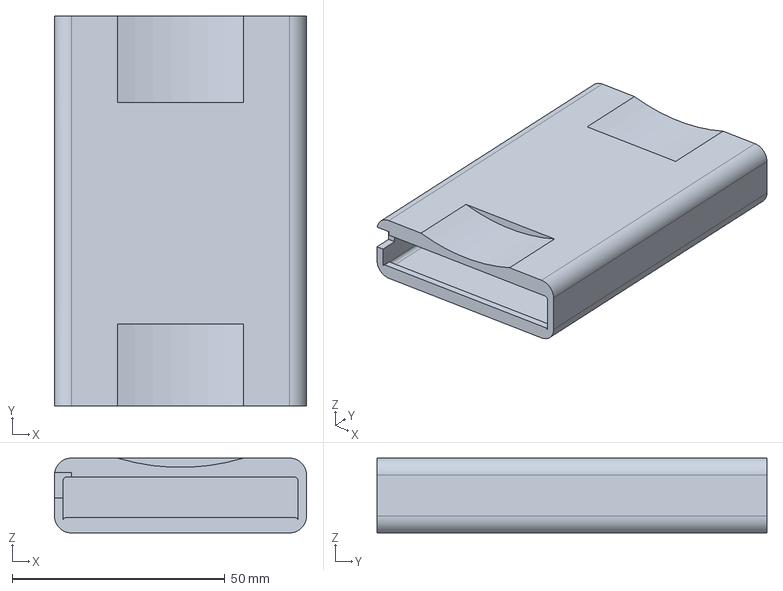
[picture p83: CAD file, 2026-08-13]
roam-touch/cad/out/bracer_pack.step
59.2 x 91.6 x 17.6 mm
