nhaynes84/roam/roam-touch/cad/out/landscape.step

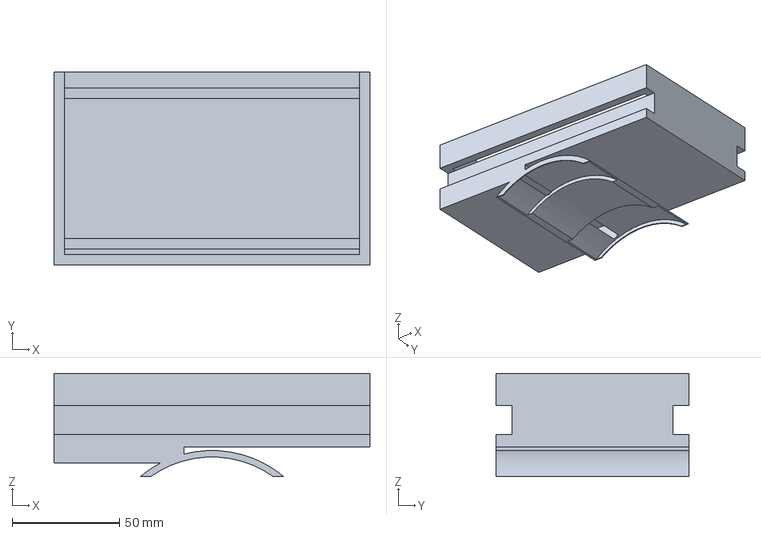
[picture p84: CAD file, 2026-08-12]
roam-touch/cad/out/landscape.step
147.0 x 90.0 x 48.1 mm
