nhaynes84/roam/roam-touch/cad/out/view_print_back.png

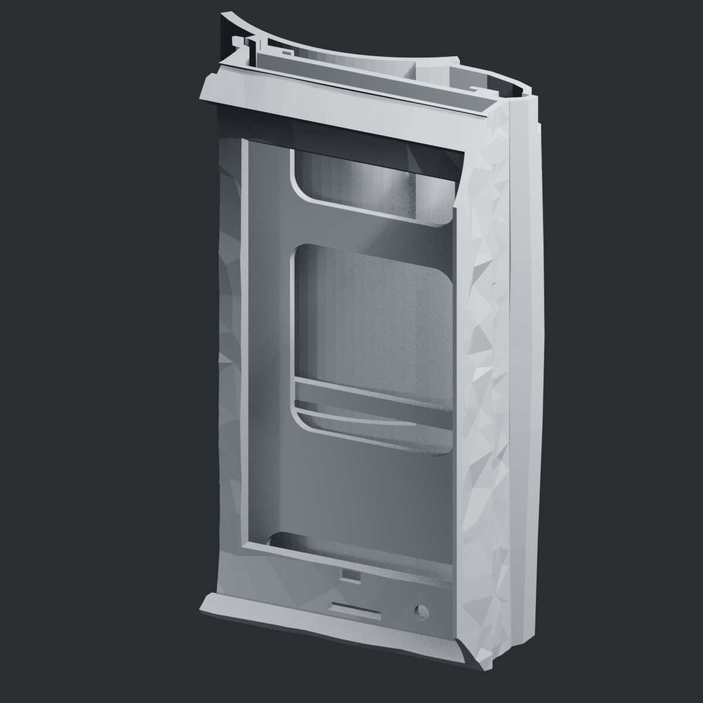
roam-touch/cad/out/view_print_back.png
