nhaynes84/roam/roam-touch/cad/out/view_print_iso.png

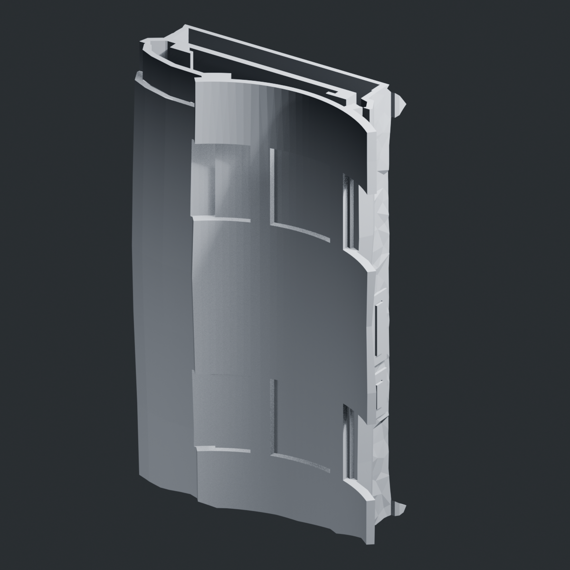
roam-touch/cad/out/view_print_iso.png
