nhaynes84/roam/roam-touch/cad/out/view_print_side.png

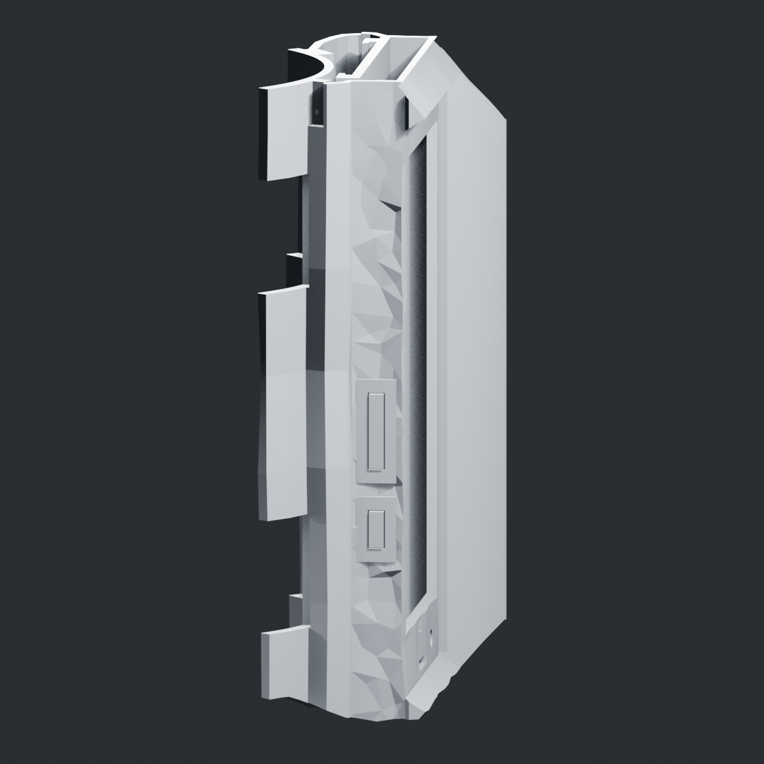
roam-touch/cad/out/view_print_side.png
