nhaynes84/roam/hardware/main-pcb/roam_main.kicad_sch

## KiCad design hardware/main-pcb/roam_main.kicad_sch (2026-07-31)

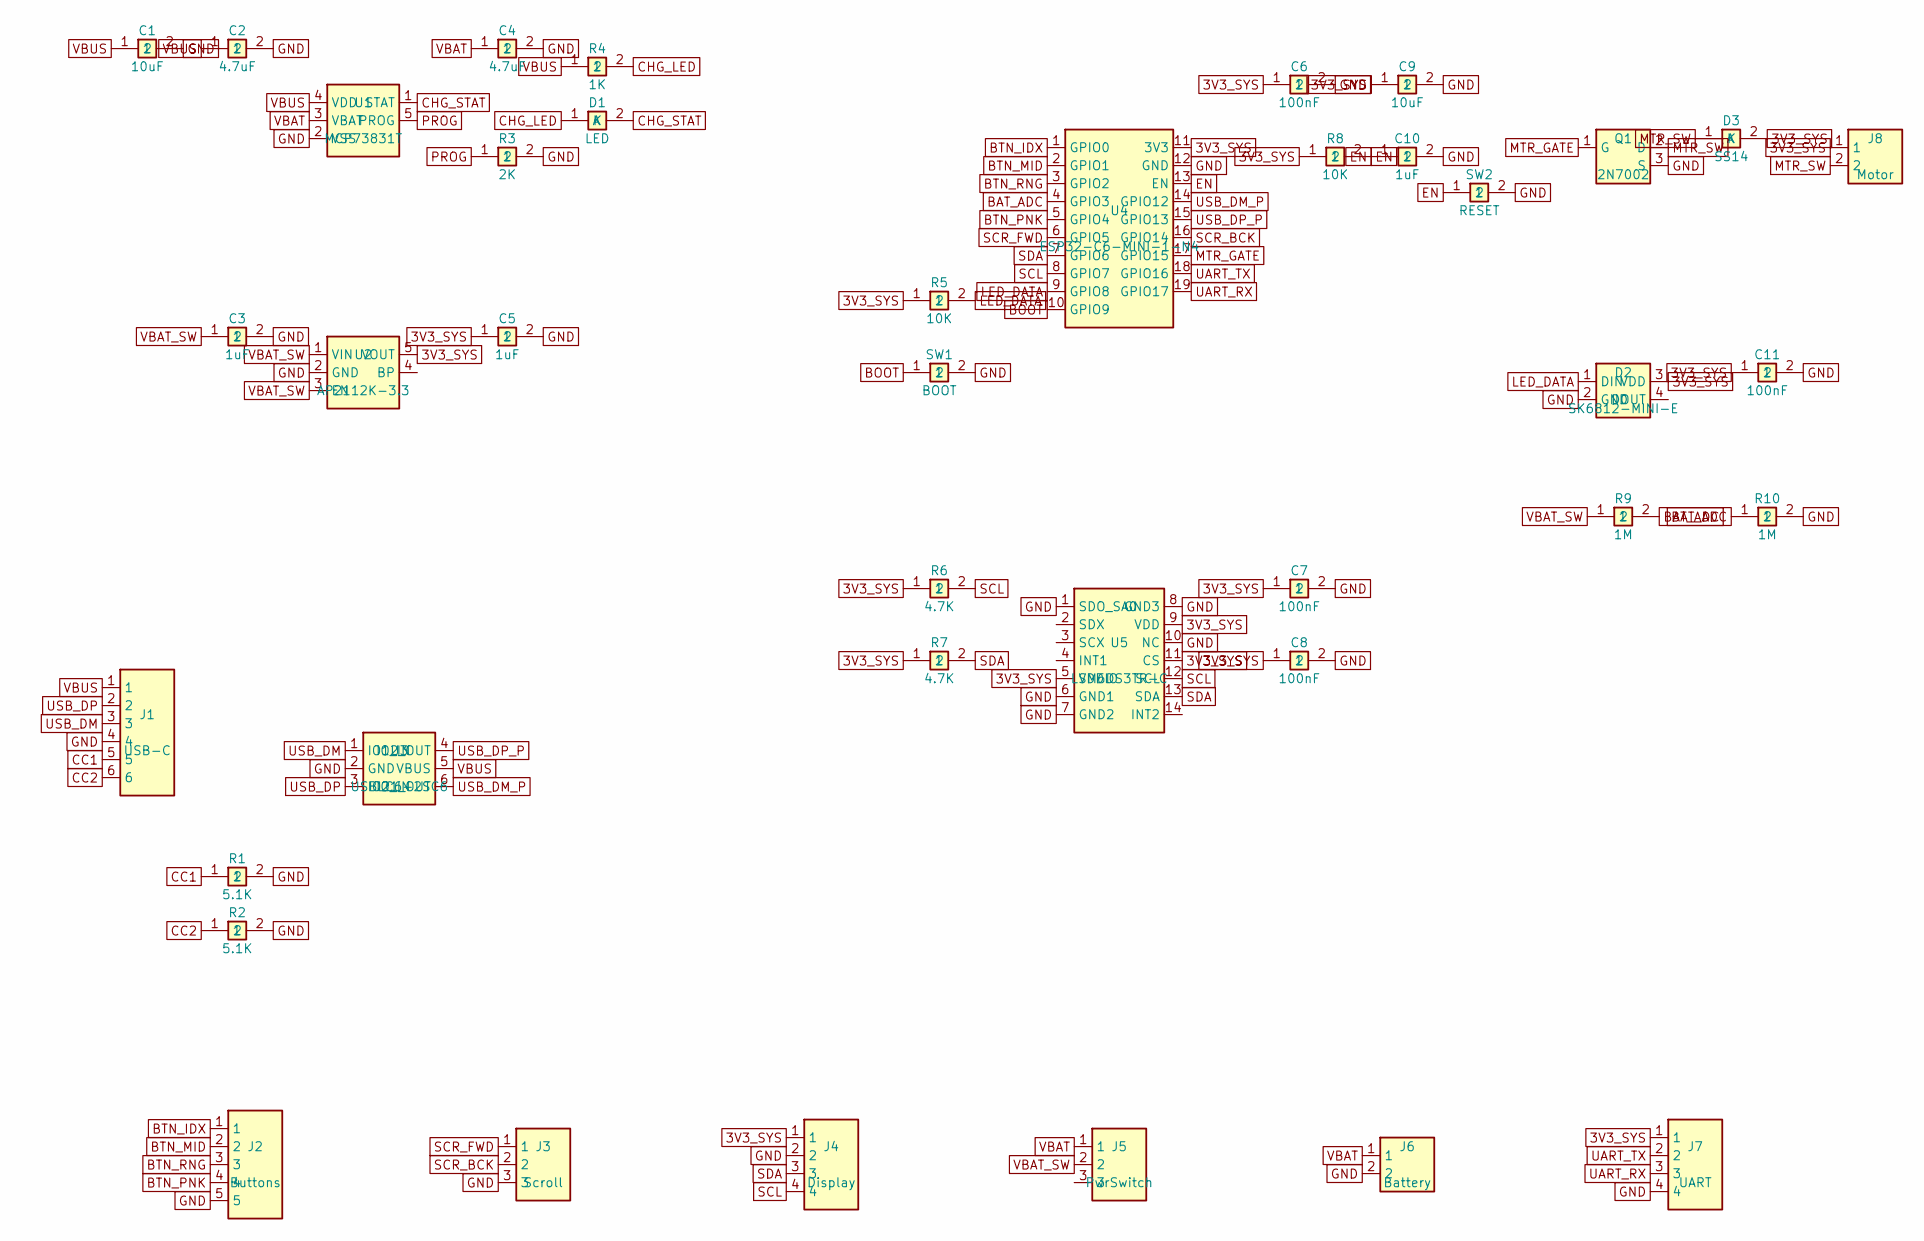
[picture p89: schematic roam_main.kicad_sch]

Parts:
C1, C9: 10uF; C_0805_2012Metric
C2, C4: 4.7uF; C_0805_2012Metric
C3, C5, C10: 1uF; C_0402_1005Metric
C6, C7, C8, C11: 100nF; C_0402_1005Metric
D1: LED; LED_0603_1608Metric
D2: SK6812-MINI-E; LED_SK6812MINI_PLCC4_3.5x3.5mm_P1.75mm
D3: SS14; D_SMA
J1: USB-C; USB_C_Receptacle_HRO_TYPE-C-31-M-12
J2: Buttons; JST_SH_SM05B-SRSS-TB_1x05-1MP_P1.00mm_Horizontal
J3: Scroll; JST_SH_SM03B-SRSS-TB_1x03-1MP_P1.00mm_Horizontal
J4: Display; JST_SH_SM04B-SRSS-TB_1x04-1MP_P1.00mm_Horizontal
J5: PwrSwitch; JST_SH_SM03B-SRSS-TB_1x03-1MP_P1.00mm_Horizontal
J6: Battery; JST_PH_B2B-PH-K_1x02_P2.00mm_Vertical
J7: UART; PinHeader_1x04_P2.54mm_Vertical
J8: Motor; JST_SH_SM02B-SRSS-TB_1x02-1MP_P1.00mm_Horizontal
Q1: 2N7002; SOT-23
R1, R2: 5.1K; R_0402_1005Metric
R3: 2K; R_0402_1005Metric
R4: 1K; R_0402_1005Metric
R5, R8: 10K; R_0402_1005Metric
R6, R7: 4.7K; R_0402_1005Metric
R9, R10: 1M; R_0402_1005Metric
SW1: BOOT; SW_Tactile_SPST_NO_Straight_CK_PTS636Sx25SMTRLFS
SW2: RESET; SW_Tactile_SPST_NO_Straight_CK_PTS636Sx25SMTRLFS
U1: MCP73831T; SOT-23-5
U2: AP2112K-3.3; SOT-23-5
U3: USBLC6-2SC6; SOT-23-6
U4: ESP32-C6-MINI-1-N4; ESP32-C6-MINI-1
U5: LSM6DS3TR-C; LGA-14_3x2.5mm_P0.5mm_LayoutBorder3x4y

Connections:
3V3_SYS: C5.1, C6.1, C7.1, C8.1, C9.1, C11.1, D2.3 (VDD), D3.2 (K), J4.1, J7.1, J8.1, R5.1, R6.1, R7.1, R8.1, U2.5 (VOUT), U4.11 (3V3), U5.5 (VDDIO), U5.9 (VDD), U5.11 (CS)
BAT_ADC: R9.2, R10.1, U4.4 (GPIO3)
BOOT: SW1.1, U4.10 (GPIO9)
BTN_IDX: J2.1, U4.1 (GPIO0)
BTN_MID: J2.2, U4.2 (GPIO1)
BTN_PNK: J2.4, U4.5 (GPIO4)
BTN_RNG: J2.3, U4.3 (GPIO2)
CC1: J1.5, R1.1
CC2: J1.6, R2.1
CHG_LED: D1.1 (A), R4.2
CHG_STAT: D1.2 (K), U1.1 (STAT)
EN: C10.1, R8.2, SW2.1, U4.13 (EN)
GND: C1.2, C2.2, C3.2, C4.2, C5.2, C6.2, C7.2, C8.2, C9.2, C10.2, C11.2, D2.2 (GND), J1.4, J2.5, J3.3, J4.2, J6.2, J7.4, Q1.3 (S), R1.2, R2.2, R3.2, R10.2, SW1.2, SW2.2, U1.2 (VSS), U2.2 (GND), U3.2 (GND), U4.12 (GND), U5.1 (SDO_SA0), U5.6 (GND1), U5.7 (GND2), U5.8 (GND3), U5.10 (NC)
LED_DATA: D2.1 (DIN), R5.2, U4.9 (GPIO8)
MTR_GATE: Q1.1 (G), U4.17 (GPIO15)
MTR_SW: D3.1 (A), J8.2, Q1.2 (D)
PROG: R3.1, U1.5 (PROG)
SCL: J4.4, R6.2, U4.8 (GPIO7), U5.12 (SCL)
SCR_BCK: J3.2, U4.16 (GPIO14)
SCR_FWD: J3.1, U4.6 (GPIO5)
SDA: J4.3, R7.2, U4.7 (GPIO6), U5.13 (SDA)
UART_RX: J7.3, U4.19 (GPIO17)
UART_TX: J7.2, U4.18 (GPIO16)
USB_DM: J1.3, U3.1 (IO1_IN)
USB_DM_P: U3.6 (IO1_OUT), U4.14 (GPIO12)
USB_DP: J1.2, U3.3 (IO2_IN)
USB_DP_P: U3.4 (IO2_OUT), U4.15 (GPIO13)
VBAT: C4.1, J5.1, J6.1, U1.3 (VBAT)
VBAT_SW: C3.1, J5.2, R9.1, U2.1 (VIN), U2.3 (EN)
VBUS: C1.1, C2.1, J1.1, R4.1, U1.4 (VDD), U3.5 (VBUS)
